adityuhkapoor/hack-mit-2026/design/pi-ui/mockup.html

# Nimbus camera UI: mockup

The Pi's 1024×600 panel in the Nimbus look (sky, pink, lime, slate; Plus Jakarta Sans). Every screen keeps its current layout and elements. This is a working prototype: tap the buttons on the panel to move through it, or jump to any screen on the left. Hold TALK to talk. Tap anywhere for a puff, and tap the viewfinder to focus.

Your camera just got an✱ Imagination ✱

✱AI CAMERA✱

shoot · it becomes one of fifty things · auto-posts

Fog rolling over a frosted field, someone holding wild chamomile

AI Camera · subject untouched, verified

POSTED

Scan to get this photo on your phone
