adityuhkapoor/hack-mit-2026/Brainstorming/HackMIT.pdf

Title | Problem | Solution | Audience & Impact | Inspiration & Research
Lego for Music Artists | Music production is locked behind expensive hardware and complicated software with a steep learning curve. This limits creativity and accessibility for beginners or low income groups wanting to learn | Modular, lego-like system that lets artists physically build and create music by snapping together interchangeable blocks for instruments, effects, tempo, mixing and more | Music Artists on the go Children Beginners | Link (https://devpost.com/software/harmoniq-p4bd9y)
AI Sticker Digi Camera/Multi Camera 3D Photos | Digital photography can feel too polished or impersonal, while alternatives like polaroids and photobooths aren't always accessible or convenient | A portable digital camera that uses AI to turn photos into personalized stickers with in-built filters and drawings AND/OR Multi camera point and shoot that click a photo at the same time - result is a photo/gif that feels like a 3D live experience | Everyone | Link #1 (https://devpost.com/software/diffuji) Link #2 (https://www.stickercamera.com/) Link #3 (https://k4mera.world/)

Other brainstorming for ideas:
Diffusion model that can recreate looks based on stuff you found on instagram and the mode selector can recreate that look for yourself

Two Parts: Hardware & Software

Hardware:
- Raspberry Pi Camera Module 3, High Quality Camera, wide-angle and autofocus camera modules
- Thermal Printer/Polaroid Printer
- Arduino Uno
- Rechargeable Battery

Electronics Diagram

Software
- World Brush: Eyedropper that captures real world textures/imagery
- Instagram Integration
- Landing Page

## Video

## Powerpoint Slides

## Script

How Does it Work - Turn Camera On - Select Mode: World Brush OR Filters - World Brush - Point at a texture and hold down a button for 3 seconds to lock it in - Then Take Picture - Then use brush to draw on picture - Filter - Select Filter - Then Take Picture - Image Processing - Press Confirm - Prints Picture Physical Format - Auto Uploads to Instagram Story/Feed - Camera Off
