adityuhkapoor/hack-mit-2026/docs/demo/video/README.md

# Demo renders for the video

Four scenes through the live pipeline on the GB10 (klein 9B, 1.0 MP), Muse choosing the format unprompted:

| Scene | Muse chose | Headline | Source photo |
|---|---|---|---|
| kids playing football | sports trading card | ROOKIE HYPE TEN | US Army / Rachel Larue, public domain |
| slurping ramen, Dōtonbori | instant noodle packet | MIDNIGHT SHOYU SLURP | Maarten Heerlien, CC BY 2.0 |
| guitarist in the woods | music album cover | FOREST SHREDDER | Mostafameraji, CC BY 4.0 |
| study area | school detention slip | SILENT DETENTION HALL | D00264450, CC BY-SA 4.0 |

`*-as-shot.jpg` is the input, `*-nimbus.jpg` the square print, `*-before-after.jpg` both side by side (1080 px
tall). The people are pixel-identical between the two — "subject unaltered · verified" on every one.
