adityuhkapoor/hack-mit-2026/archive/pitch/hackmit-sketch.pdf

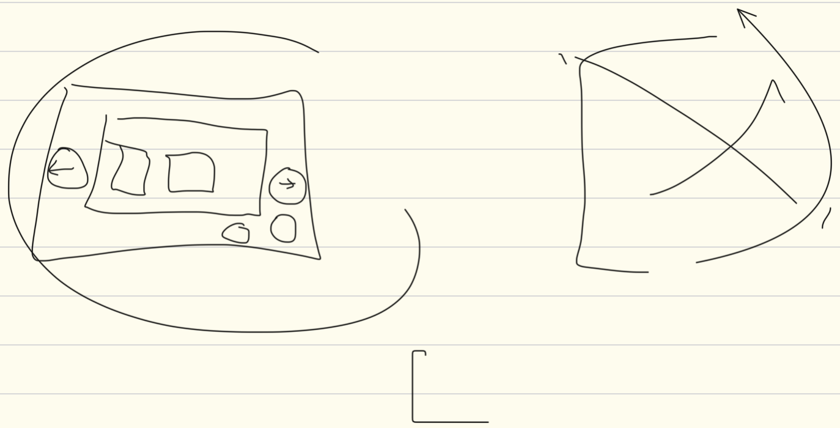
[picture p2: figure]
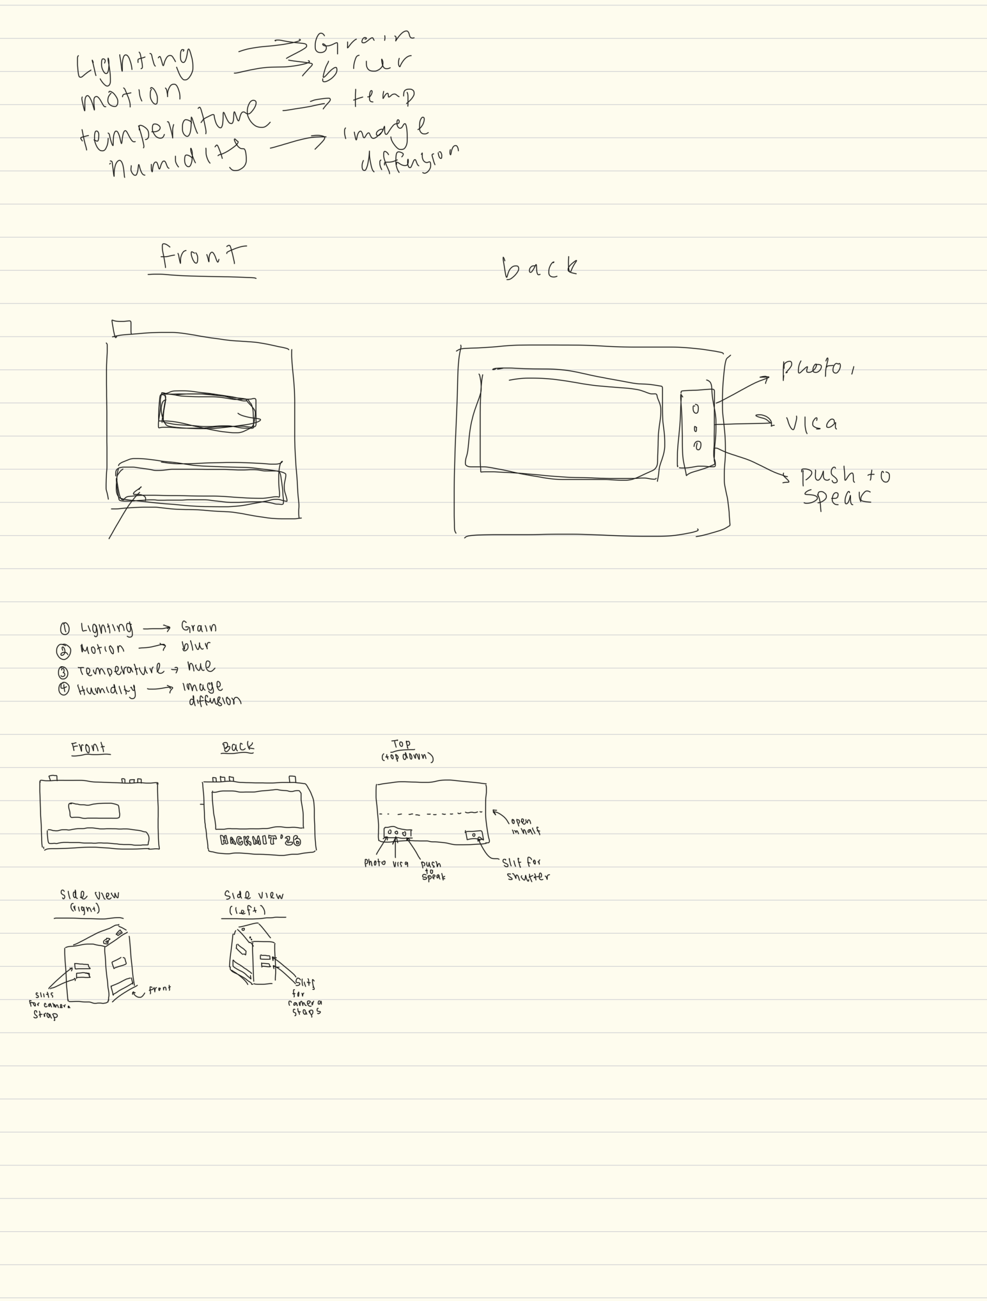
[picture p3: page 2]
