adityuhkapoor/hack-mit-2026/Brainstorming/Pasted 2026-09-18 at 11.16.00 PM.png

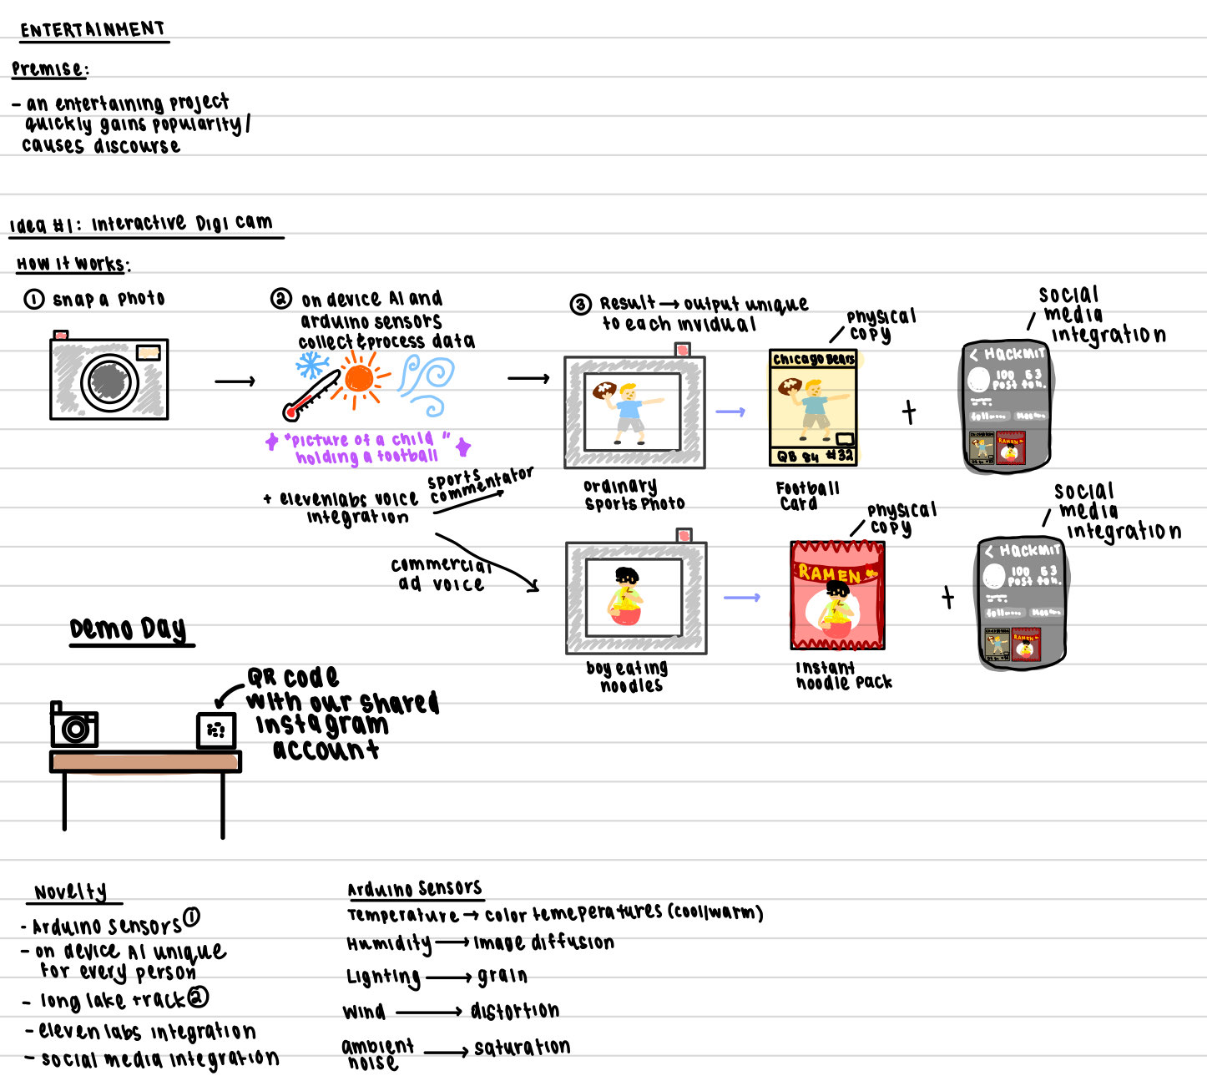
Brainstorming/Pasted 2026-09-18 at 11.16.00 PM.png
