adityuhkapoor/hack-mit-2026/design/modular-camera/cutaway.png

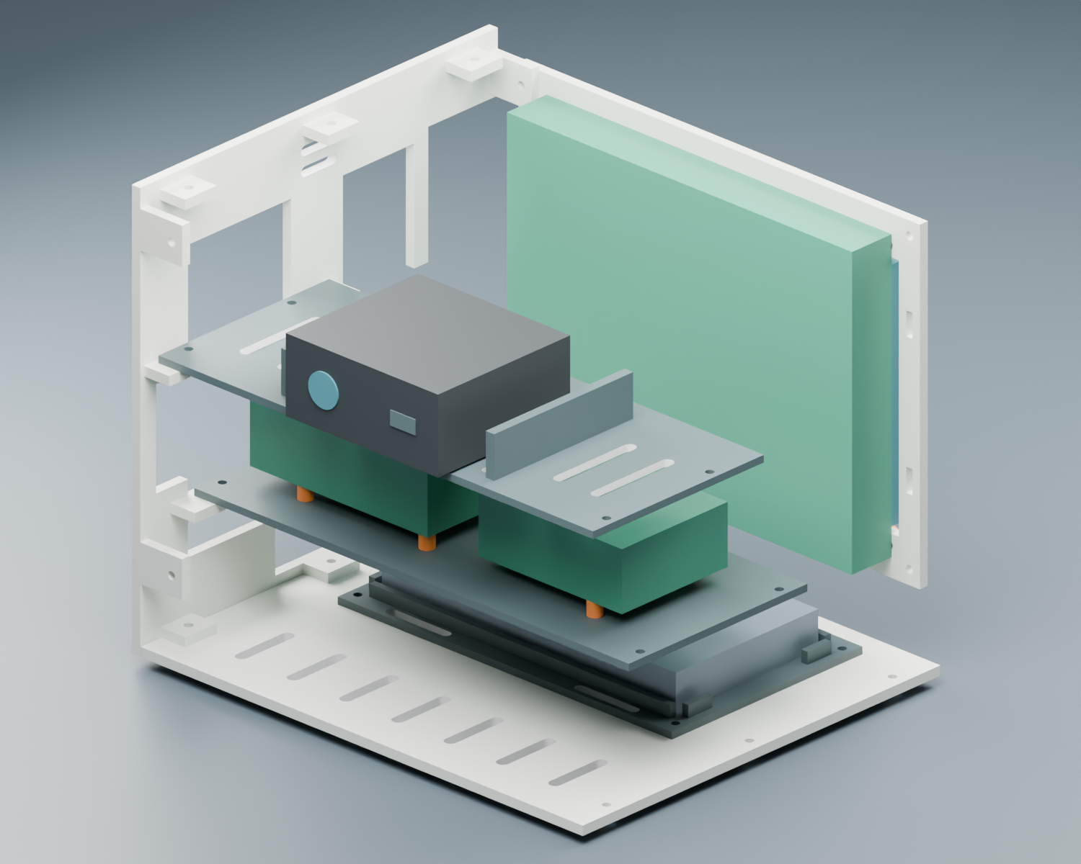
design/modular-camera/cutaway.png
