adityuhkapoor/hack-mit-2026/docs/demo/dusk_0_as_shot.jpg

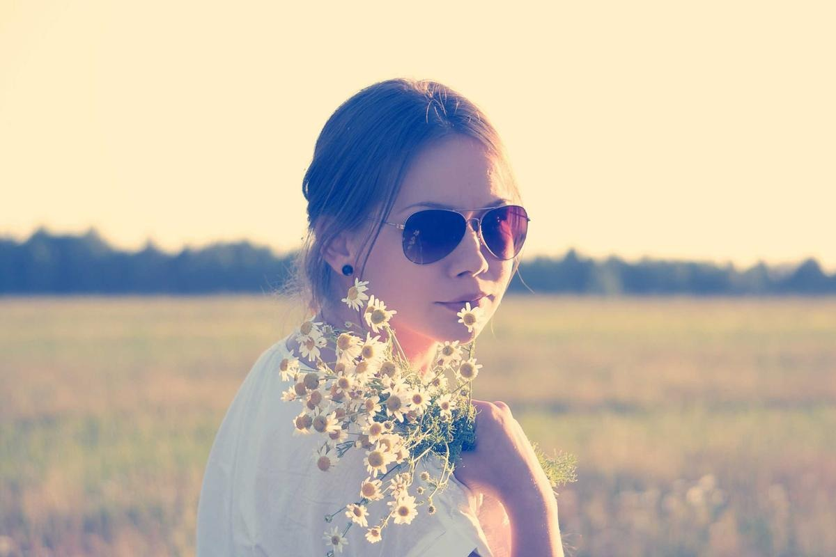
docs/demo/dusk_0_as_shot.jpg
