adityuhkapoor/hack-mit-2026/docs/demo/dusk_0_card.jpg

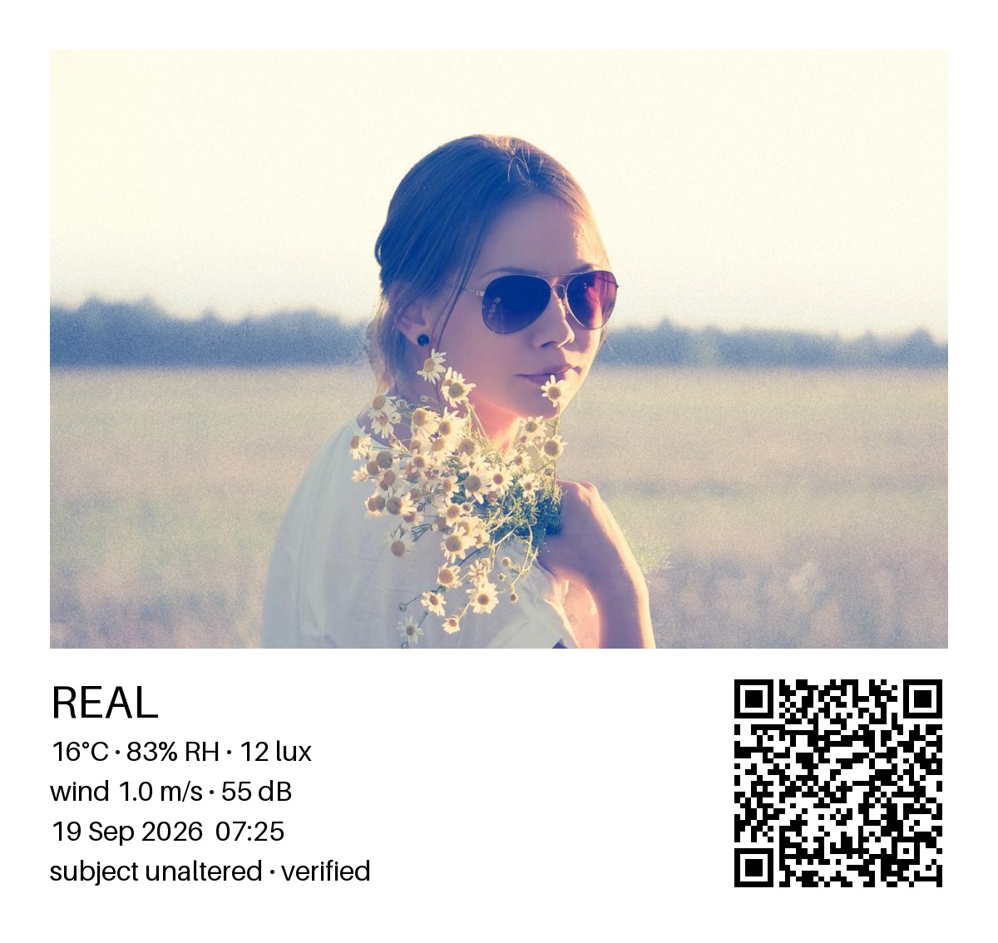
docs/demo/dusk_0_card.jpg
