adityuhkapoor/hack-mit-2026/docs/demo/dusk_0_photo.jpg

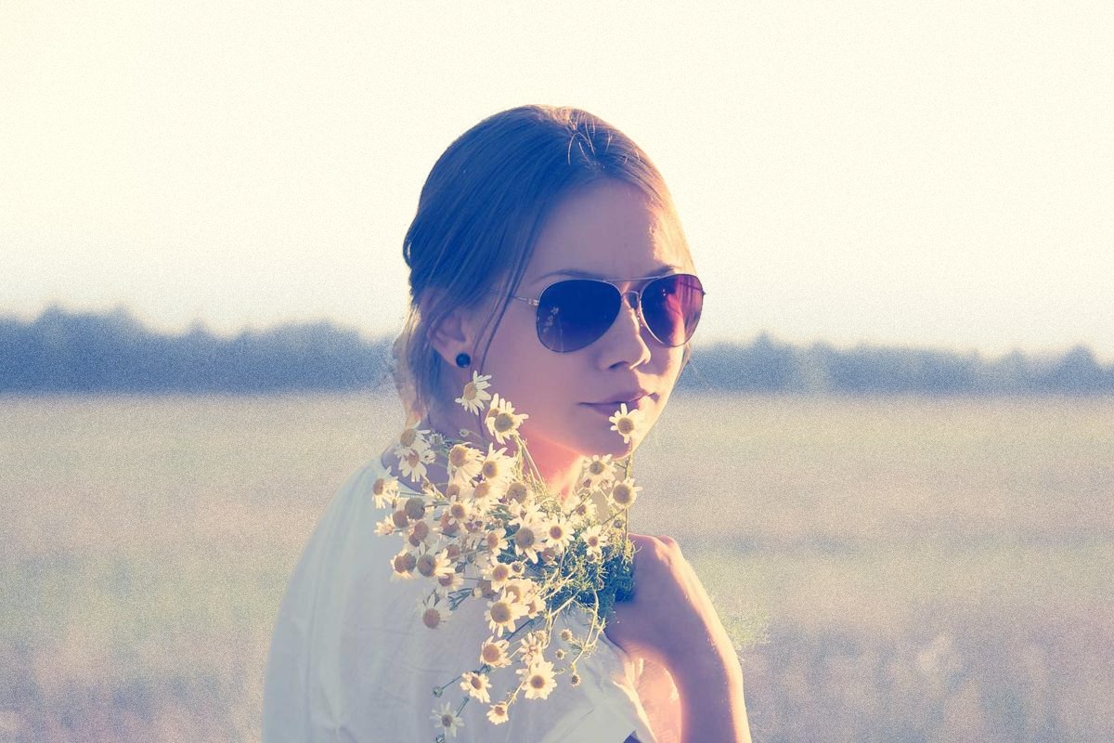
docs/demo/dusk_0_photo.jpg
