adityuhkapoor/hack-mit-2026/docs/demo/dusk_1_card.jpg

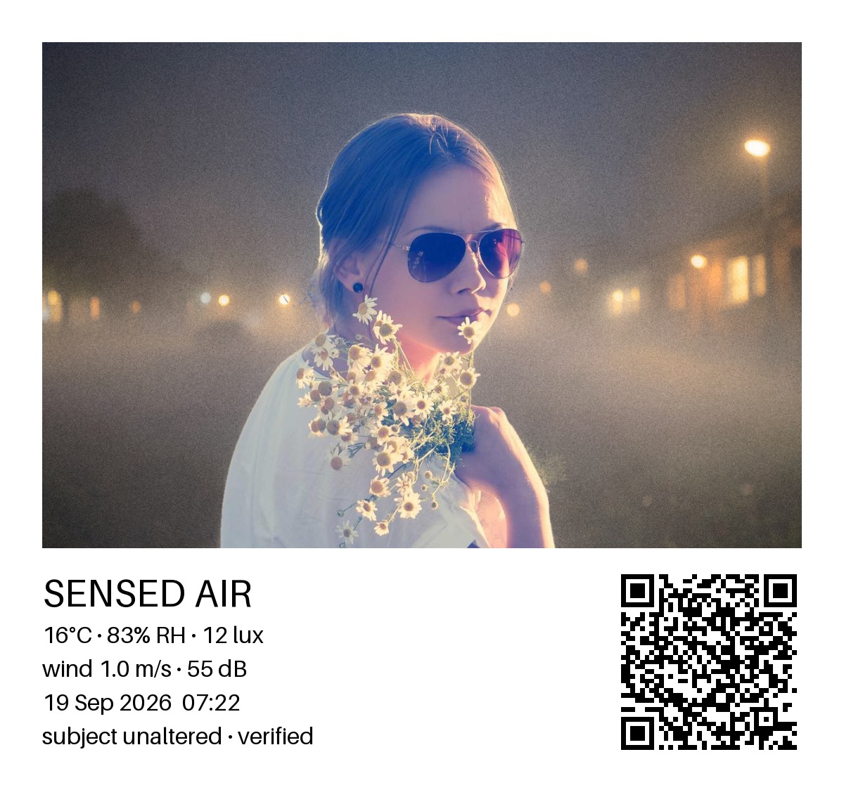
docs/demo/dusk_1_card.jpg
