adityuhkapoor/hack-mit-2026/docs/demo/dusk_1_photo.jpg

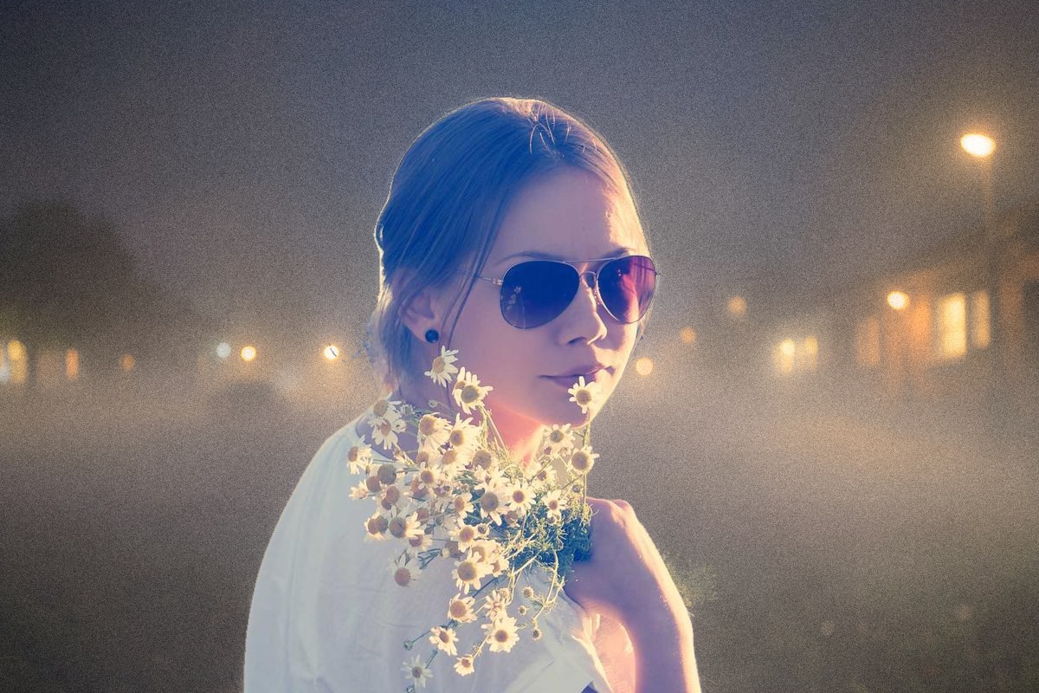
docs/demo/dusk_1_photo.jpg
