adityuhkapoor/hack-mit-2026/docs/demo/dusk_2_photo.jpg

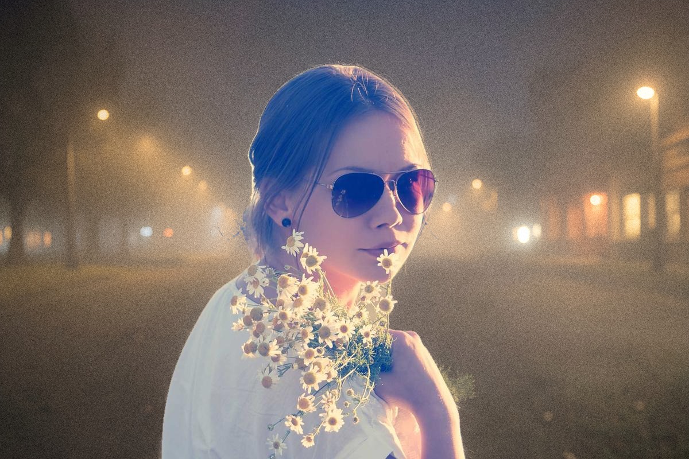
docs/demo/dusk_2_photo.jpg
