adityuhkapoor/hack-mit-2026/docs/demo/fog_0_photo.jpg

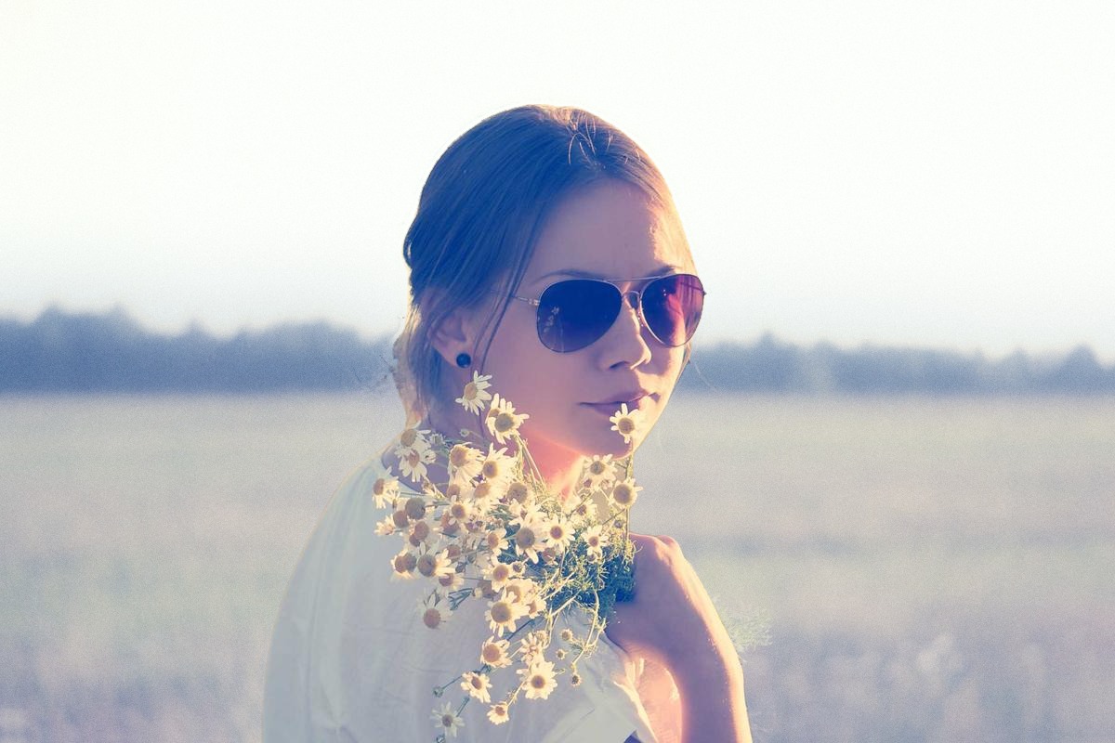
docs/demo/fog_0_photo.jpg
