adityuhkapoor/hack-mit-2026/docs/demo/fog_1_card.jpg

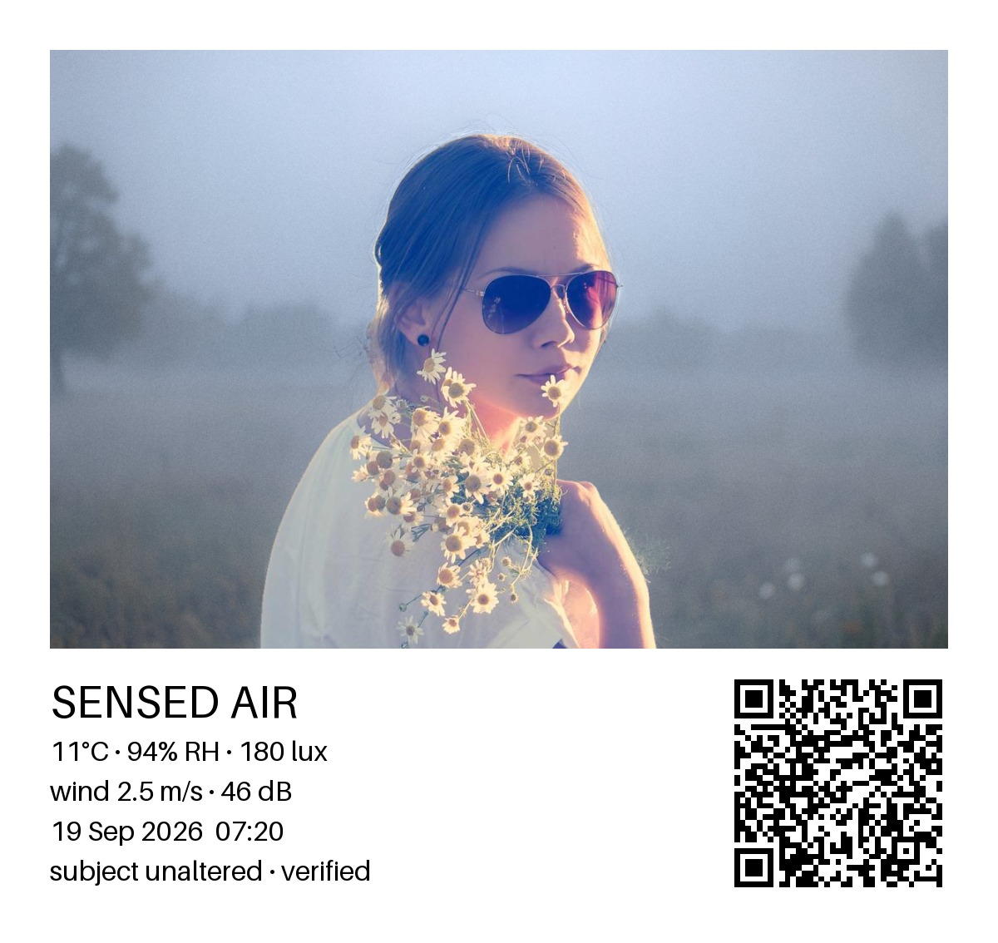
docs/demo/fog_1_card.jpg
