adityuhkapoor/hack-mit-2026/docs/demo/fog_1_photo.jpg

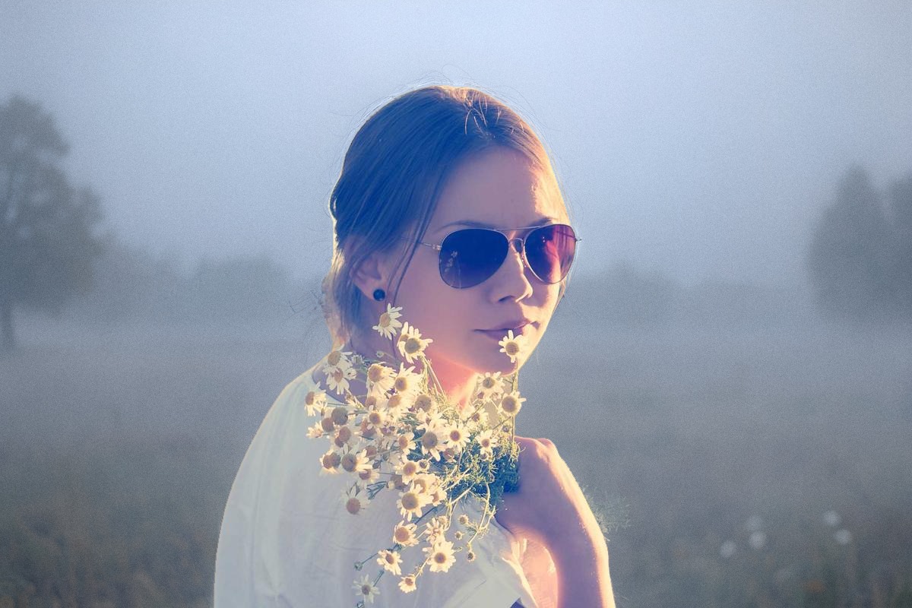
docs/demo/fog_1_photo.jpg
