adityuhkapoor/hack-mit-2026/docs/demo/fog_2_card.jpg

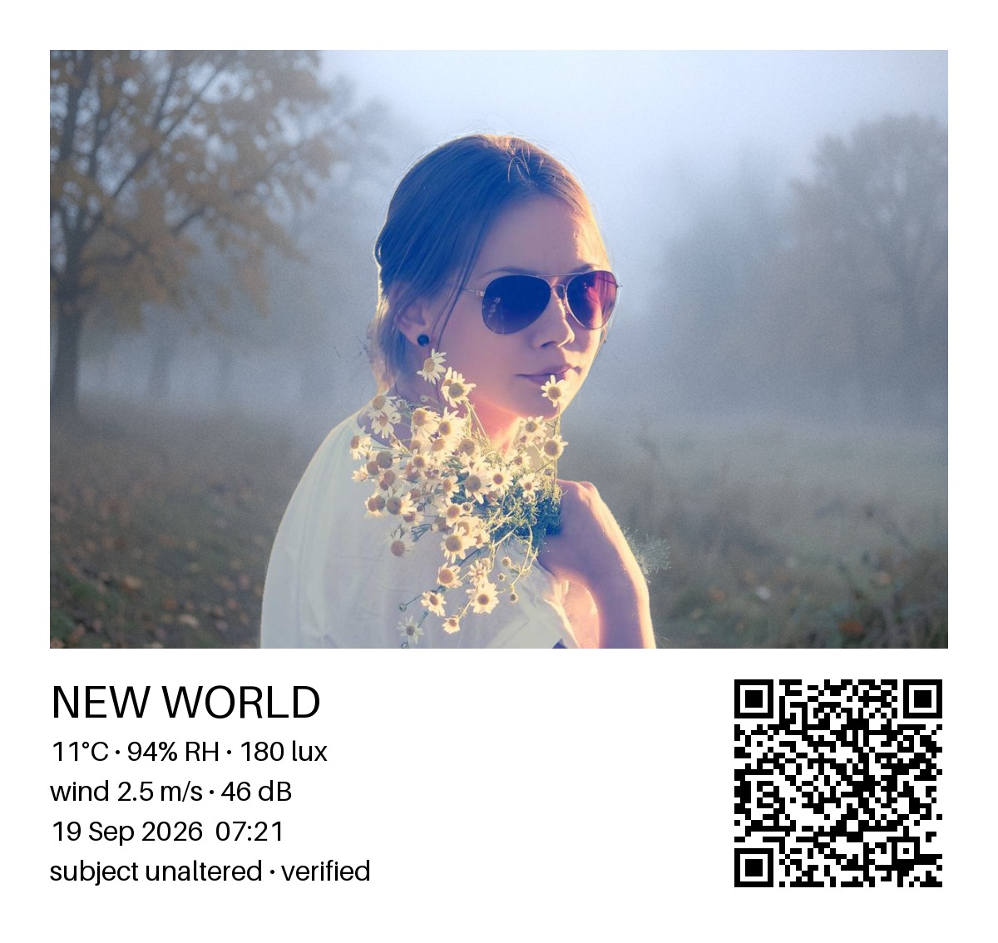
docs/demo/fog_2_card.jpg
