adityuhkapoor/hack-mit-2026/docs/demo/fog_2_photo.jpg

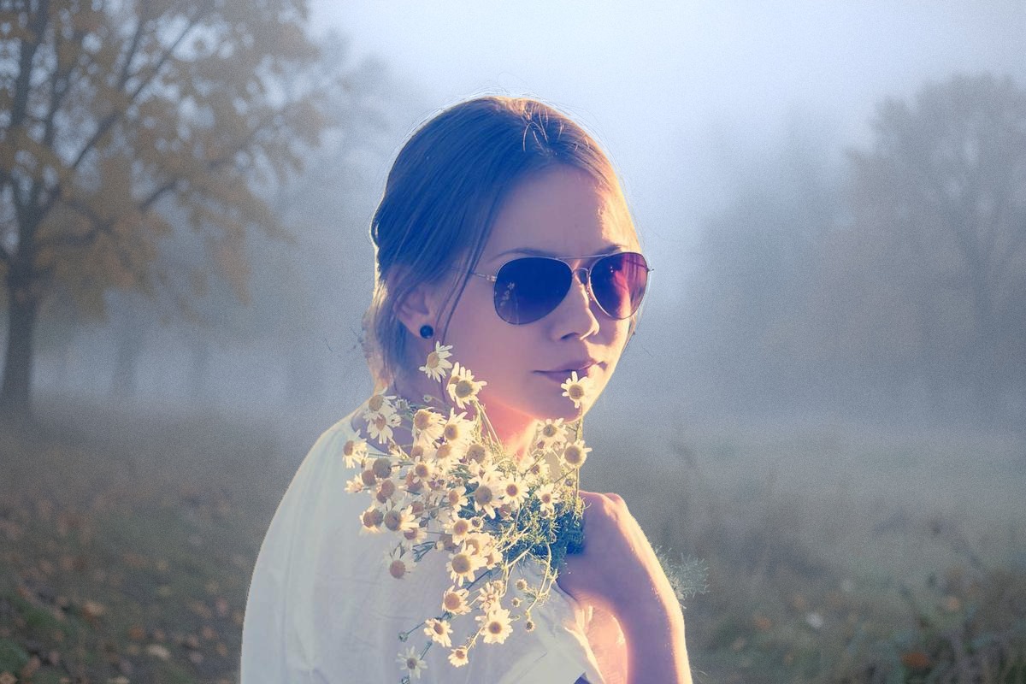
docs/demo/fog_2_photo.jpg
