adityuhkapoor/hack-mit-2026/docs/demo/heat_0_card.jpg

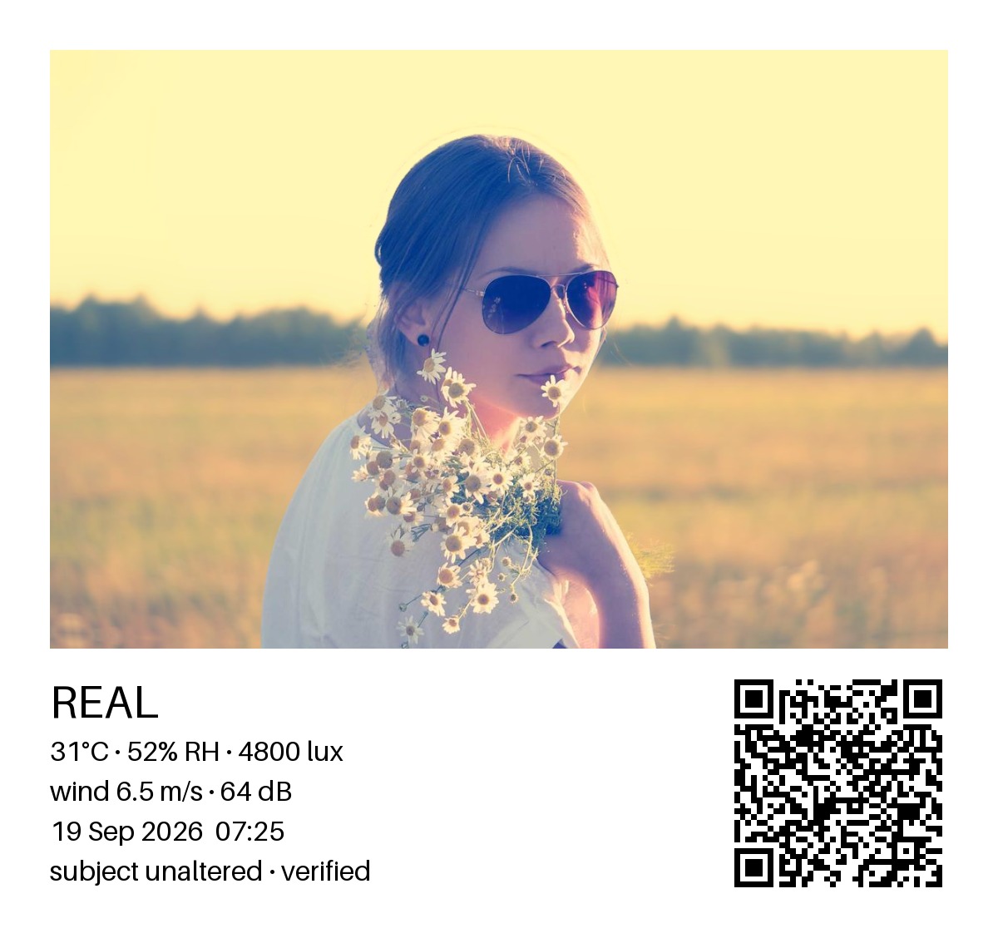
docs/demo/heat_0_card.jpg
