adityuhkapoor/hack-mit-2026/docs/demo/heat_1_card.jpg

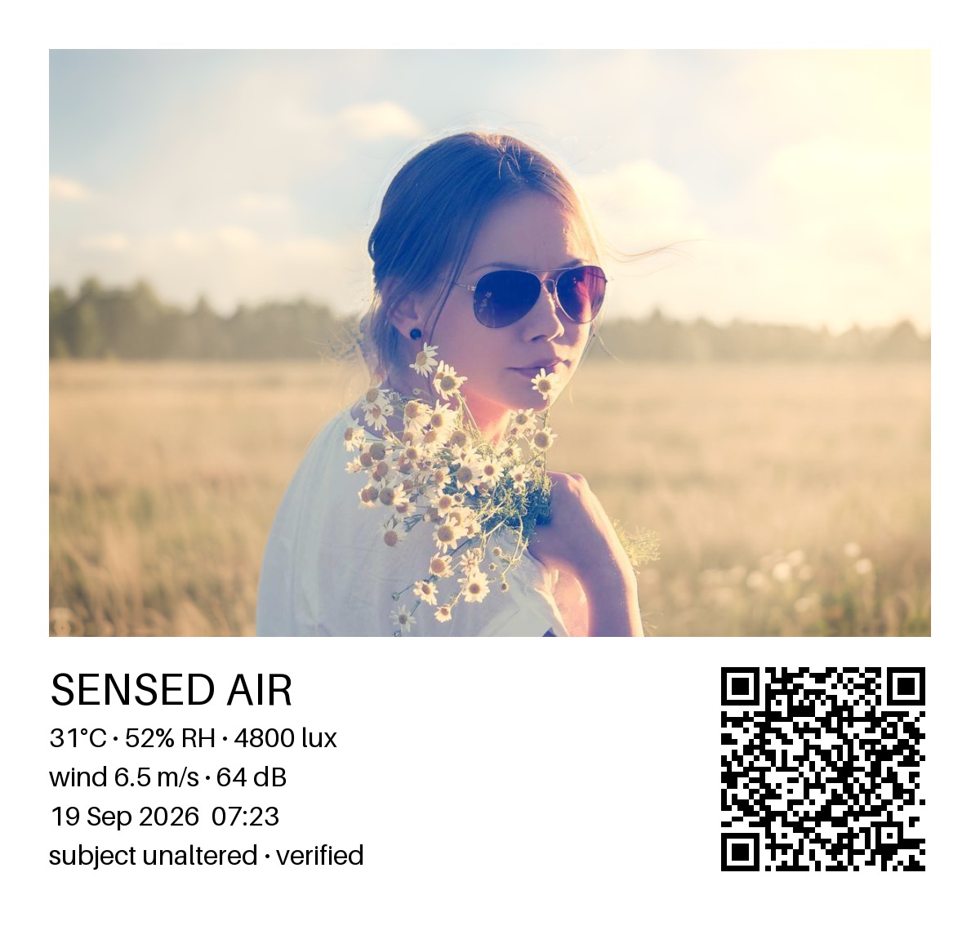
docs/demo/heat_1_card.jpg
