adityuhkapoor/hack-mit-2026/docs/demo/heat_1_photo.jpg

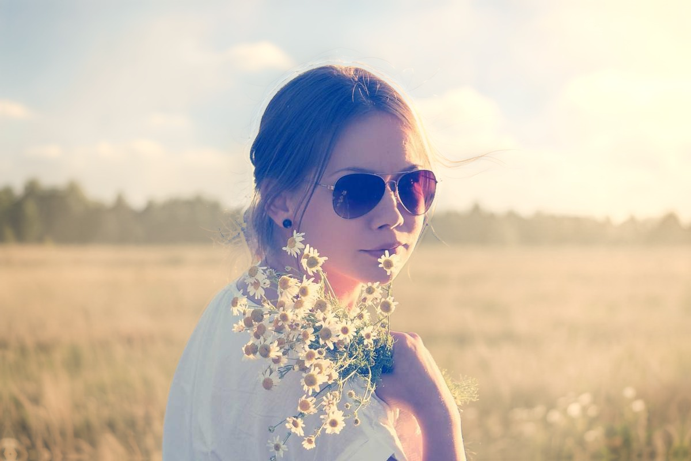
docs/demo/heat_1_photo.jpg
