adityuhkapoor/hack-mit-2026/docs/demo/heat_2_card.jpg

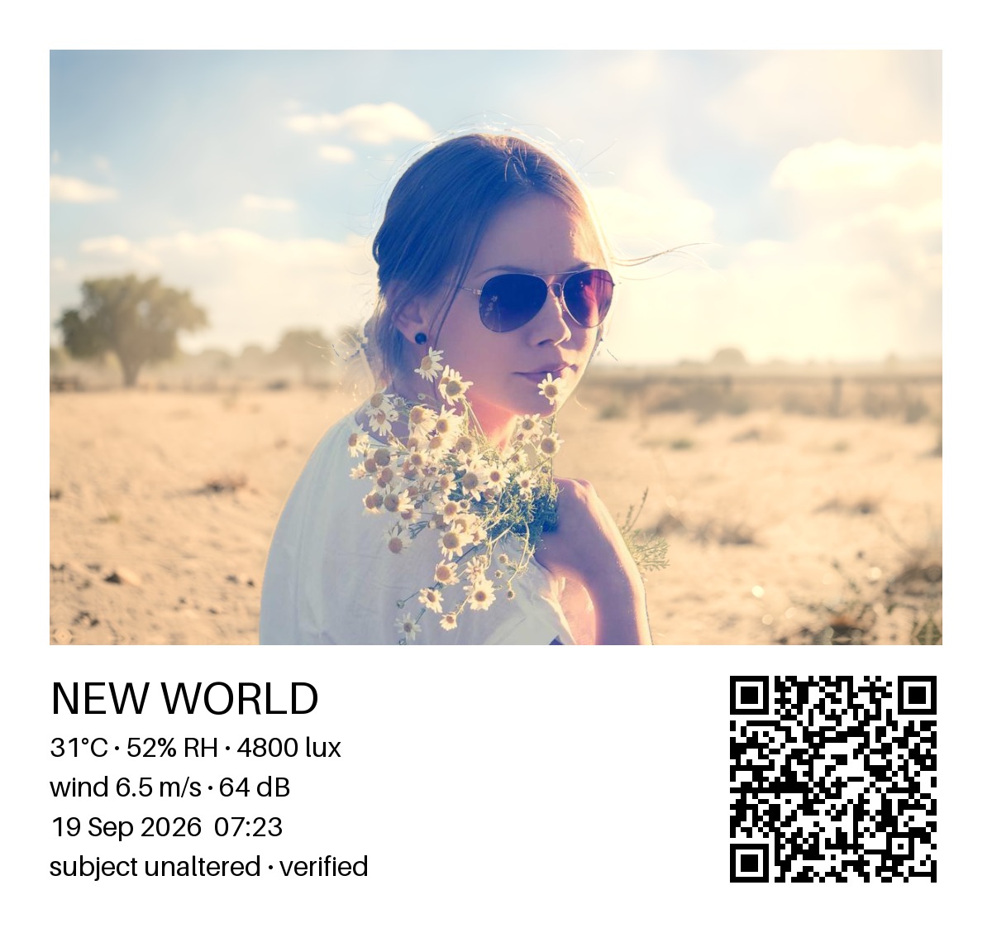
docs/demo/heat_2_card.jpg
