adityuhkapoor/hack-mit-2026/docs/demo/heat_2_photo.jpg

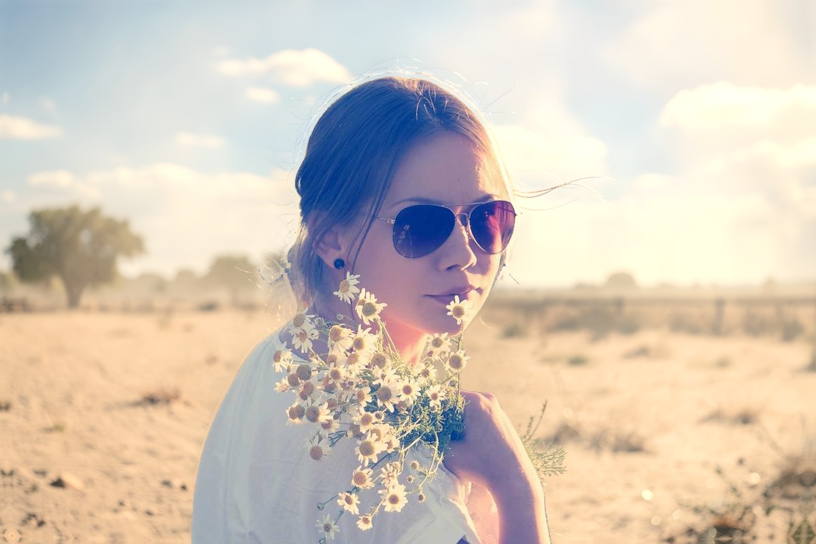
docs/demo/heat_2_photo.jpg
