adityuhkapoor/hack-mit-2026/docs/demo/pi-panel.png

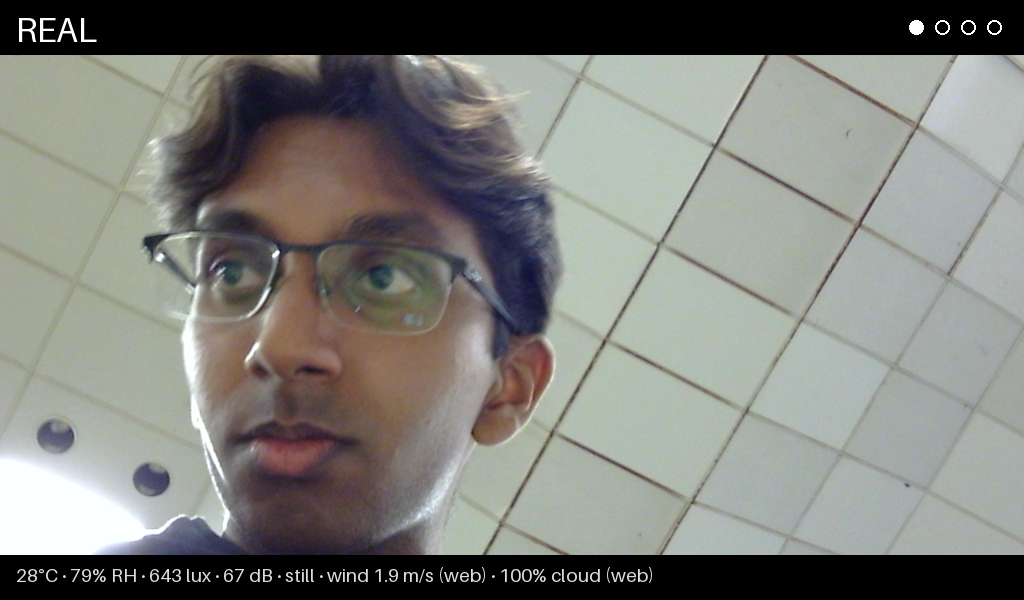
docs/demo/pi-panel.png
