adityuhkapoor/hack-mit-2026/docs/demo/sheet.jpg

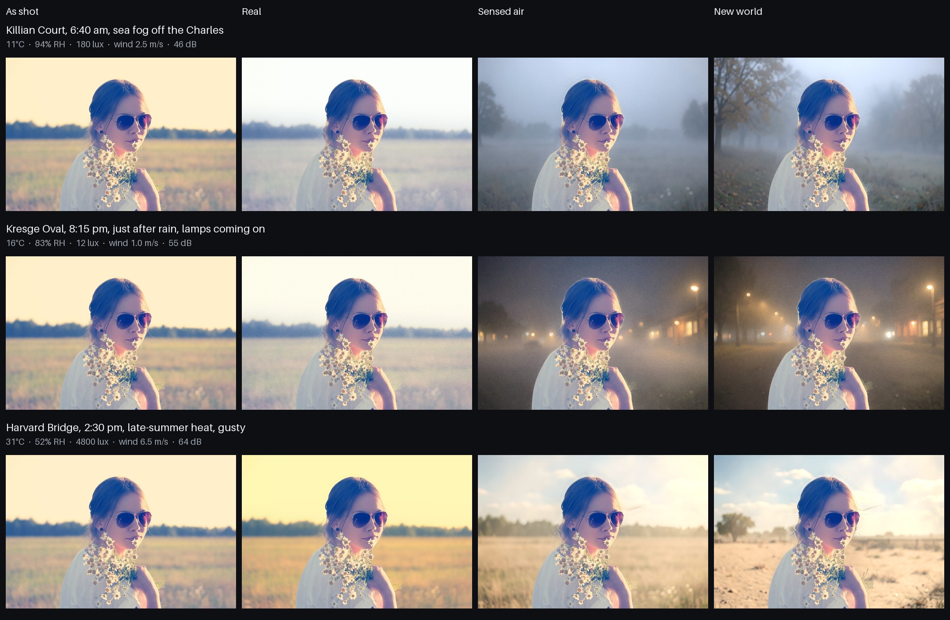
docs/demo/sheet.jpg
