adityuhkapoor/hack-mit-2026/docs/demo/video/football-as-shot.jpg

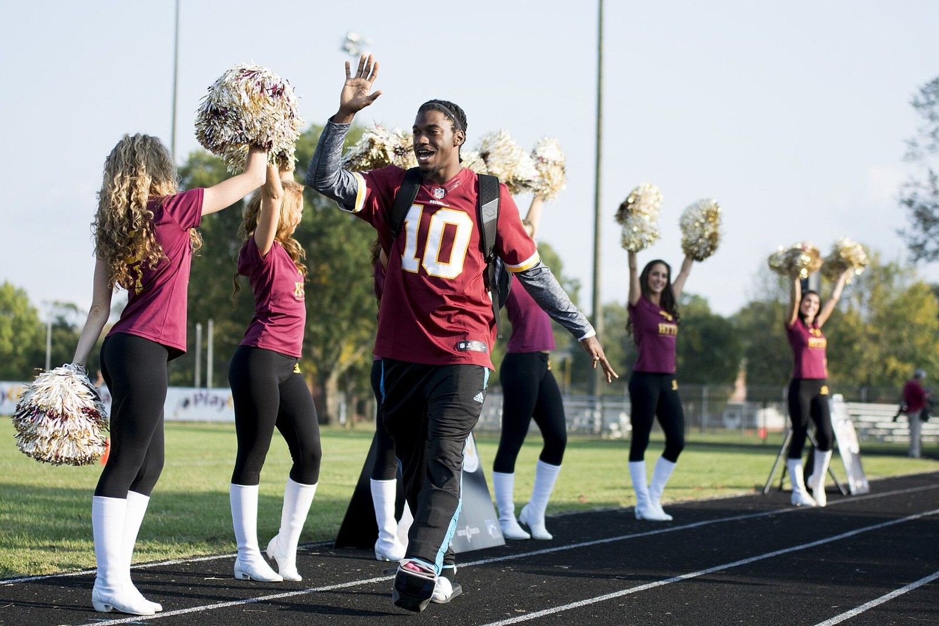
docs/demo/video/football-as-shot.jpg
