adityuhkapoor/hack-mit-2026/docs/demo/video/football-before-after.jpg

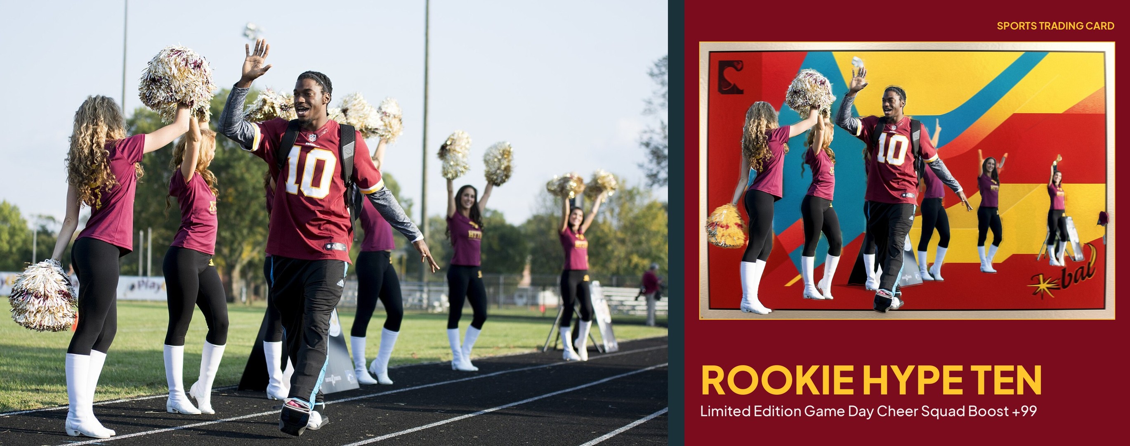
docs/demo/video/football-before-after.jpg
