adityuhkapoor/hack-mit-2026/docs/demo/video/football-nimbus.jpg

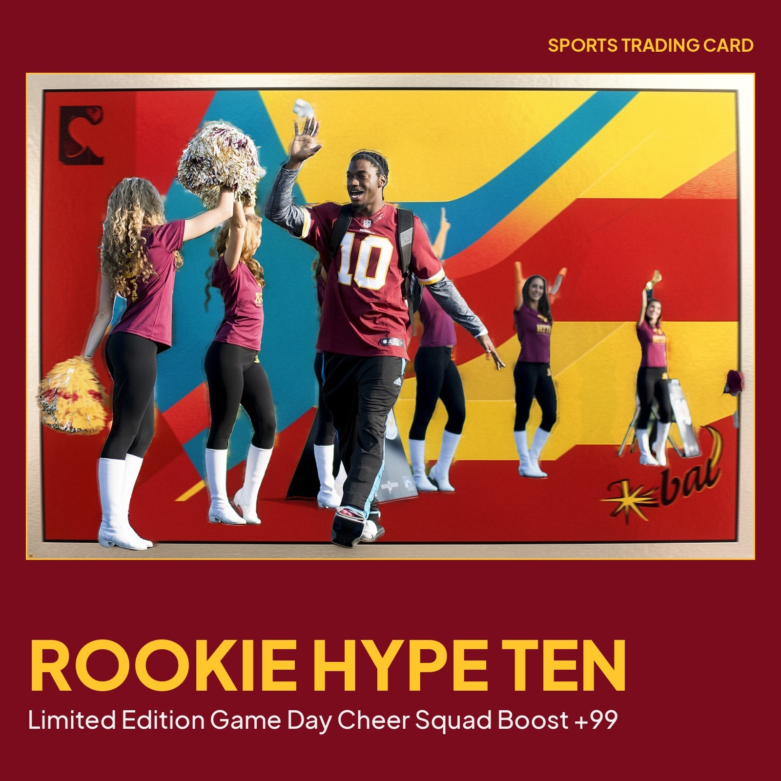
docs/demo/video/football-nimbus.jpg
