adityuhkapoor/hack-mit-2026/docs/demo/video/guitar-as-shot.jpg

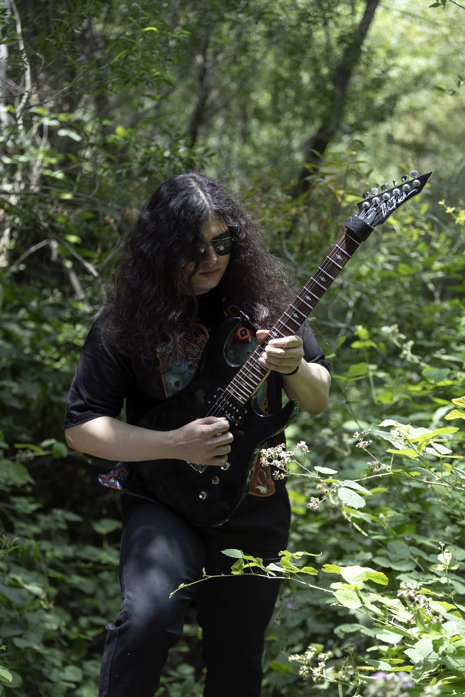
docs/demo/video/guitar-as-shot.jpg
