adityuhkapoor/hack-mit-2026/docs/demo/video/guitar-before-after.jpg

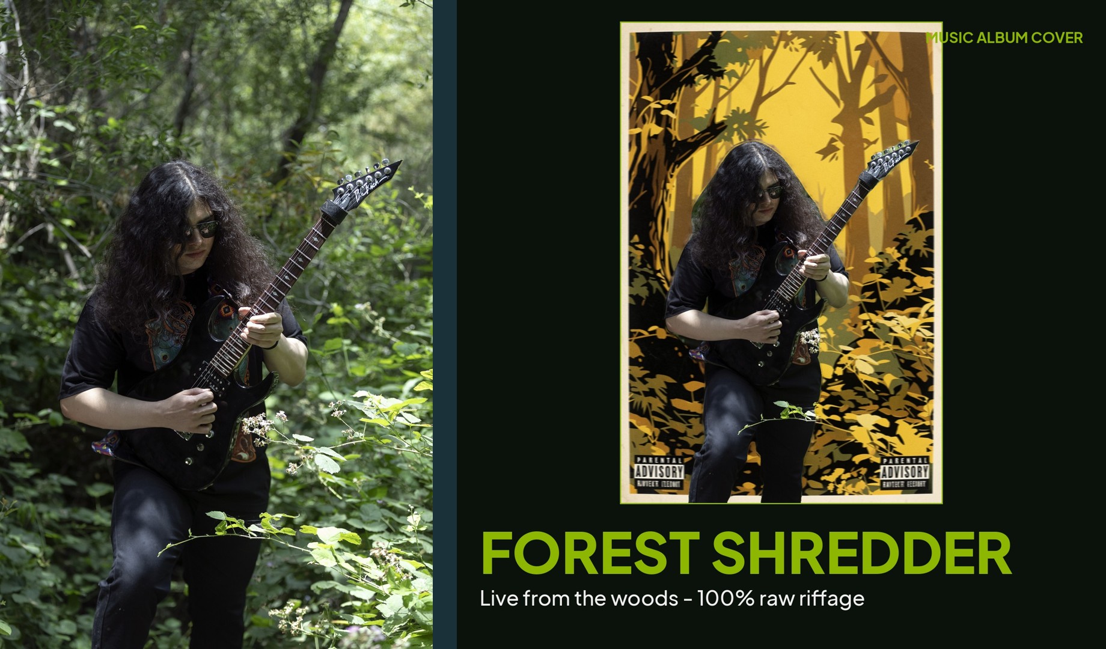
docs/demo/video/guitar-before-after.jpg
