adityuhkapoor/hack-mit-2026/docs/demo/video/guitar-nimbus.jpg

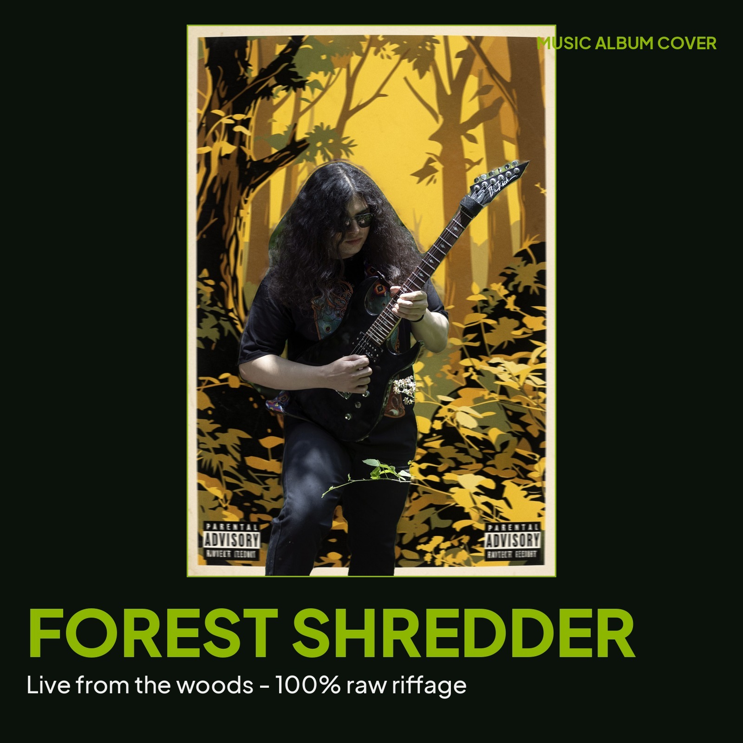
docs/demo/video/guitar-nimbus.jpg
