adityuhkapoor/hack-mit-2026/docs/demo/video/ramen-as-shot.jpg

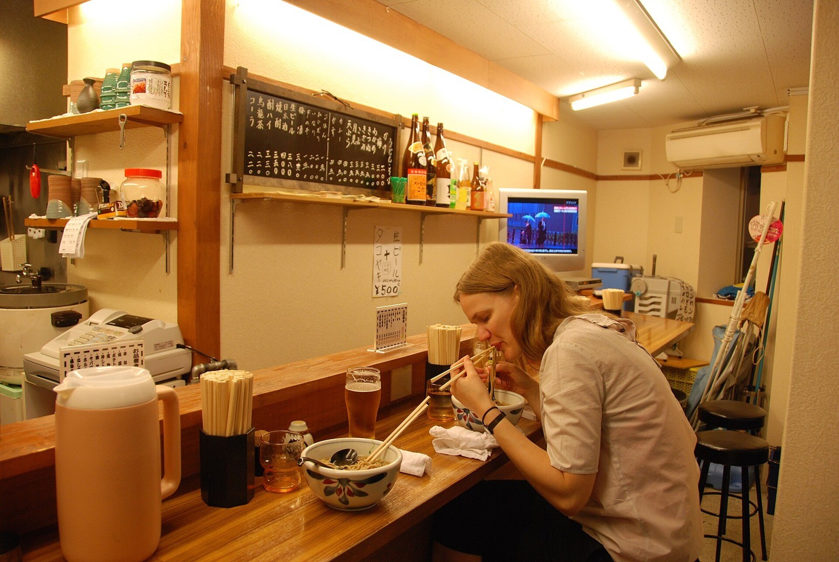
docs/demo/video/ramen-as-shot.jpg
