adityuhkapoor/hack-mit-2026/docs/demo/video/ramen-before-after.jpg

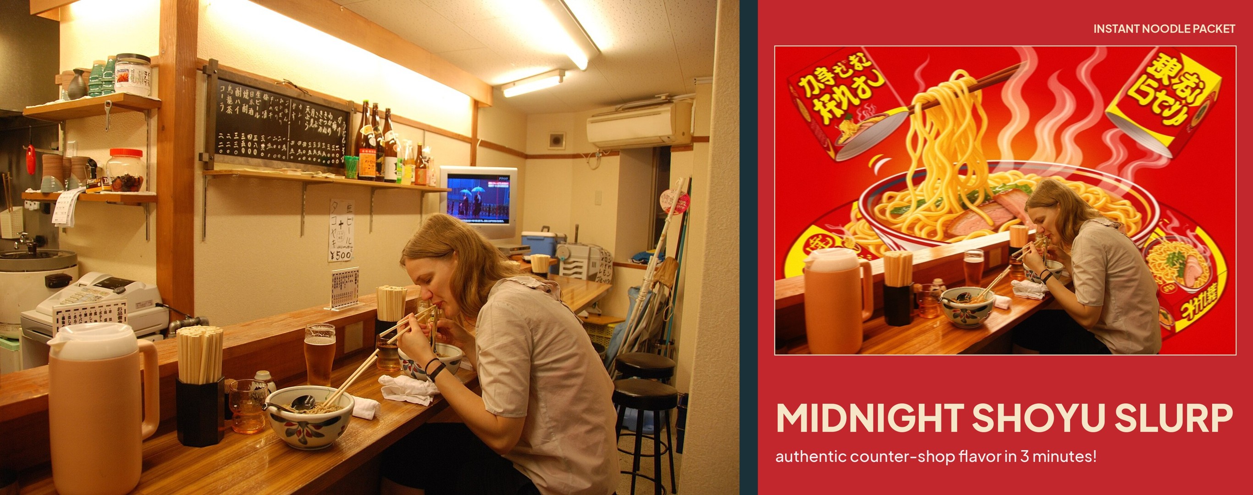
docs/demo/video/ramen-before-after.jpg
