adityuhkapoor/hack-mit-2026/docs/demo/video/ramen-nimbus.jpg

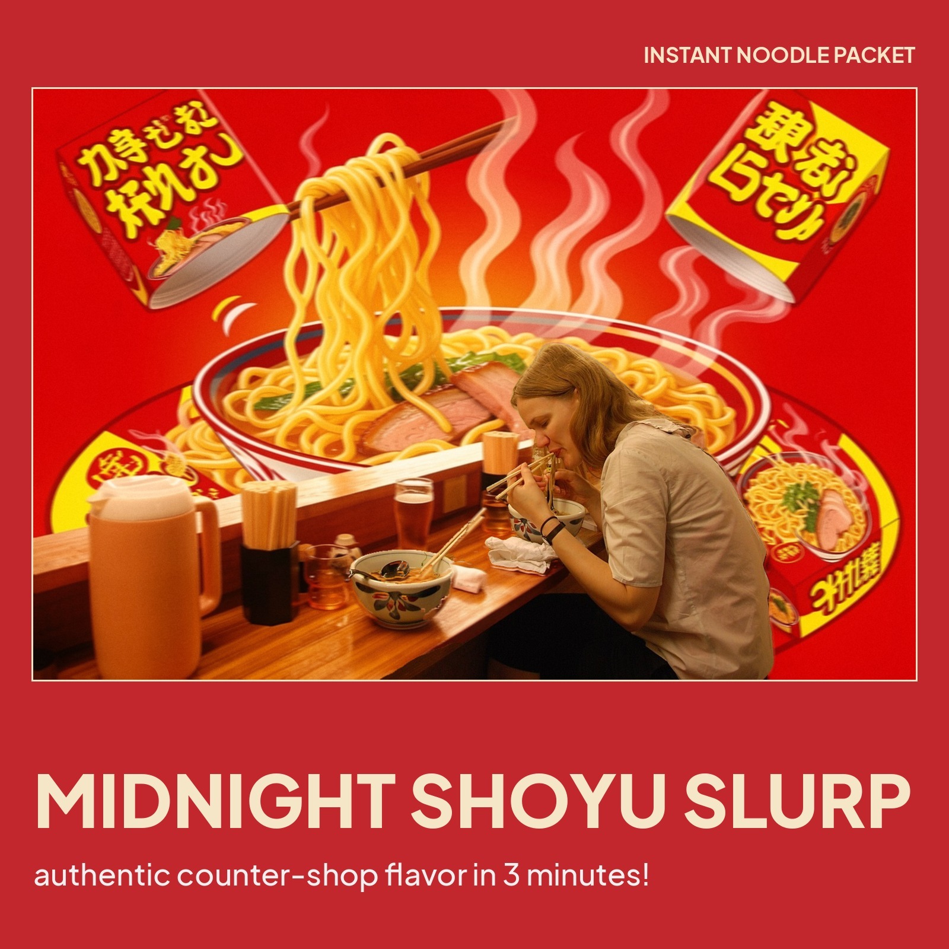
docs/demo/video/ramen-nimbus.jpg
