adityuhkapoor/hack-mit-2026/docs/demo/video/study-as-shot.jpg

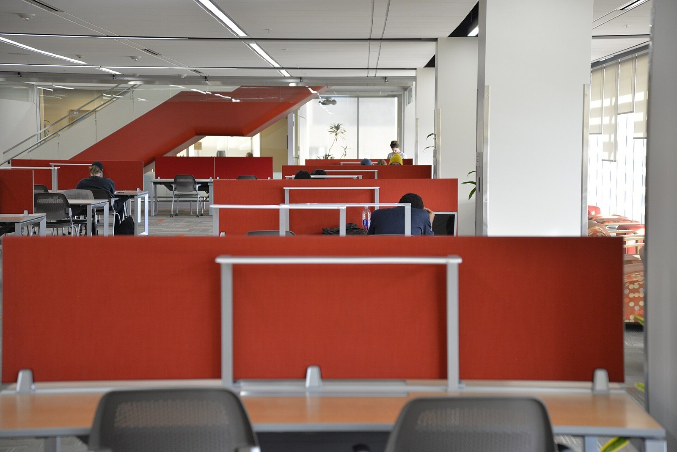
docs/demo/video/study-as-shot.jpg
