adityuhkapoor/hack-mit-2026/docs/demo/video/study-before-after.jpg

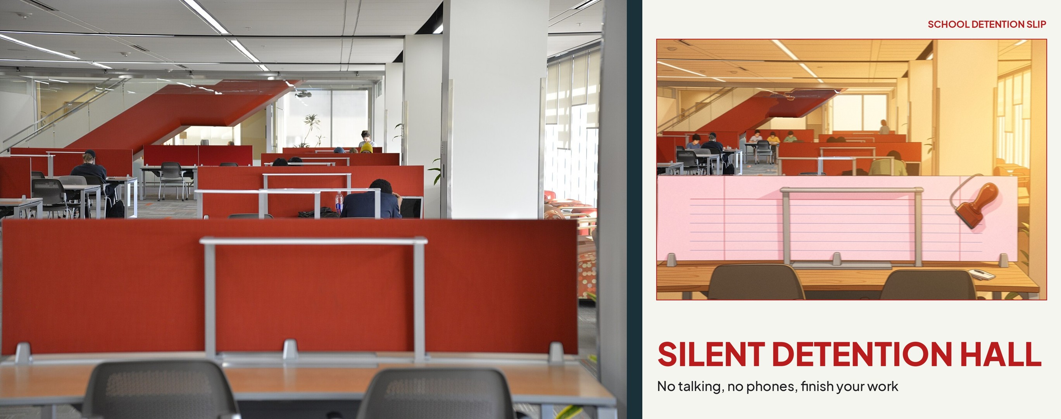
docs/demo/video/study-before-after.jpg
