adityuhkapoor/hack-mit-2026/docs/demo/video/study-nimbus.jpg

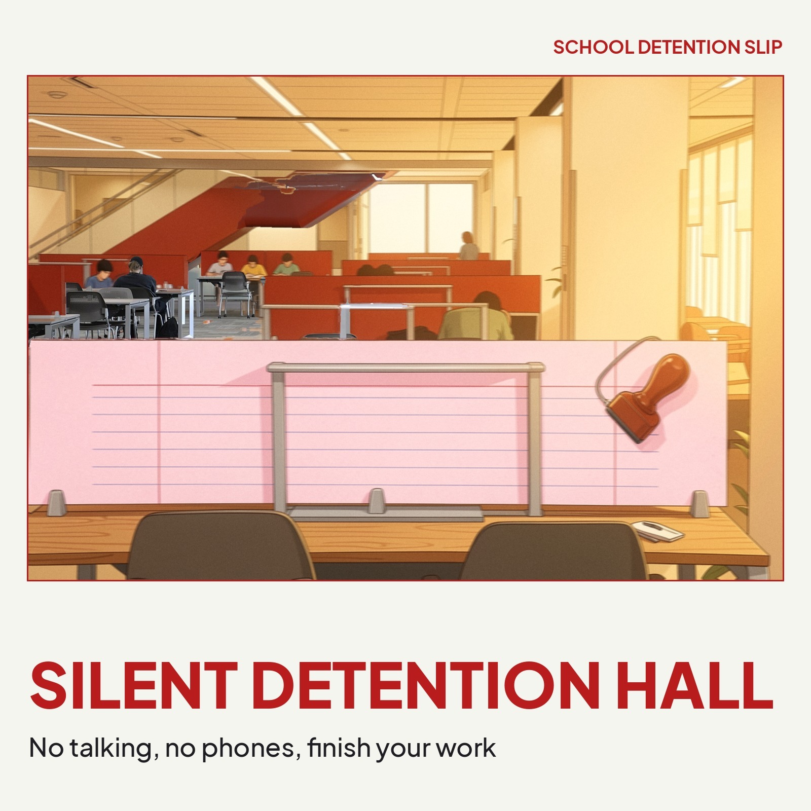
docs/demo/video/study-nimbus.jpg
