adityuhkapoor/hack-mit-2026/Photos/DSC00272-Enhanced-NR.JPG

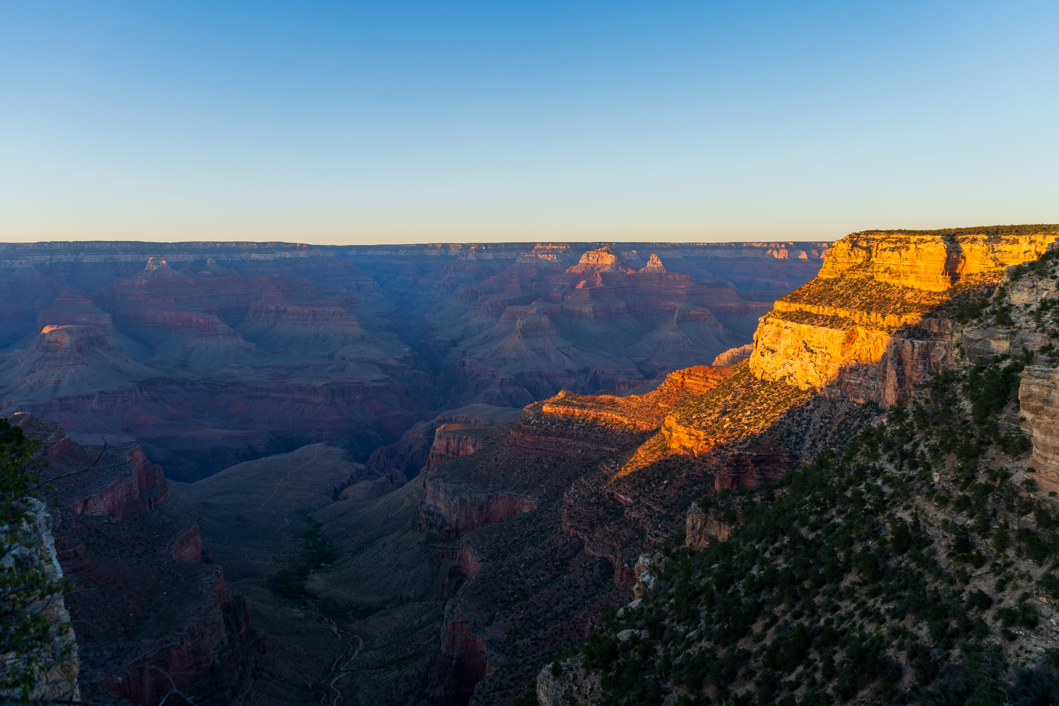
Photos/DSC00272-Enhanced-NR.JPG
