adityuhkapoor/hack-mit-2026/Photos/DSC06684-Enhanced-NR.JPG

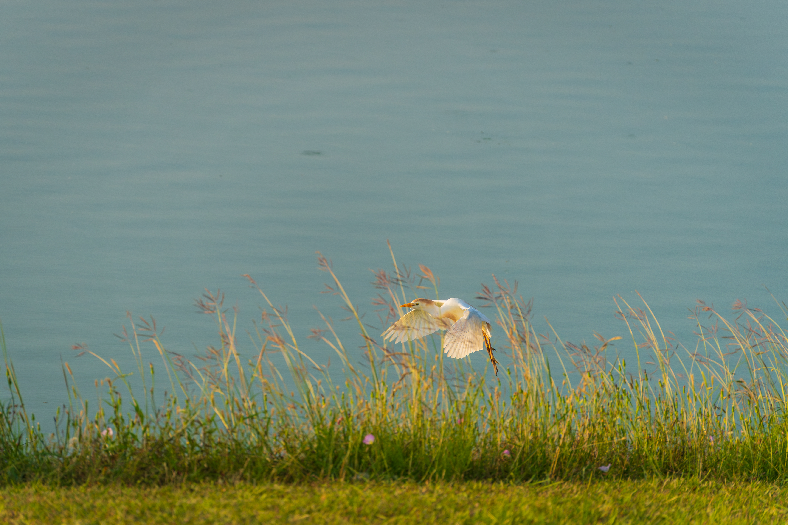
Photos/DSC06684-Enhanced-NR.JPG
