adityuhkapoor/hack-mit-2026/Photos/looks/_DSC7022-Enhanced-NR/00_original.jpg

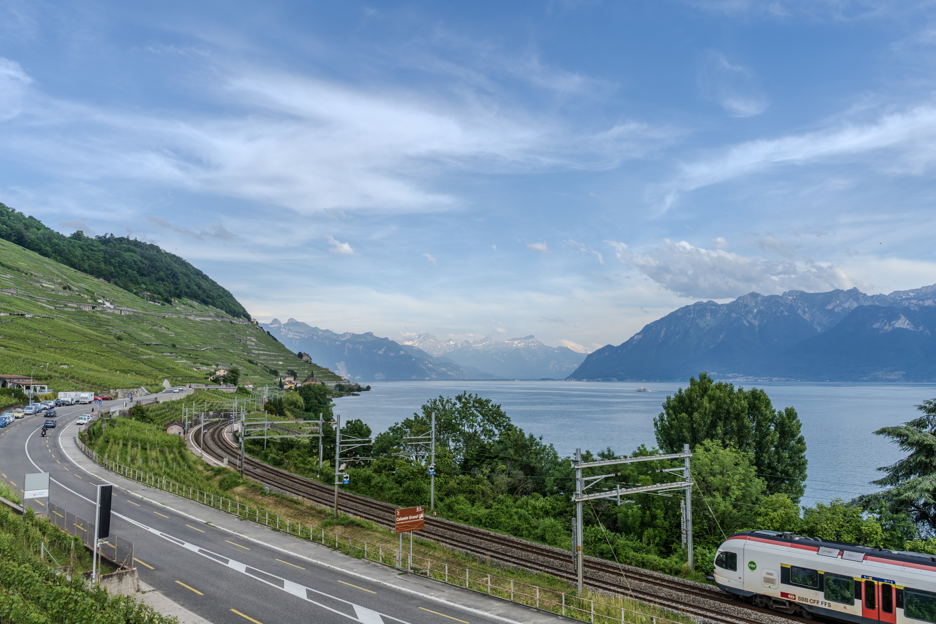
Photos/looks/_DSC7022-Enhanced-NR/00_original.jpg
