adityuhkapoor/hack-mit-2026/Photos/looks/_DSC7022-Enhanced-NR/06_digicam.jpg

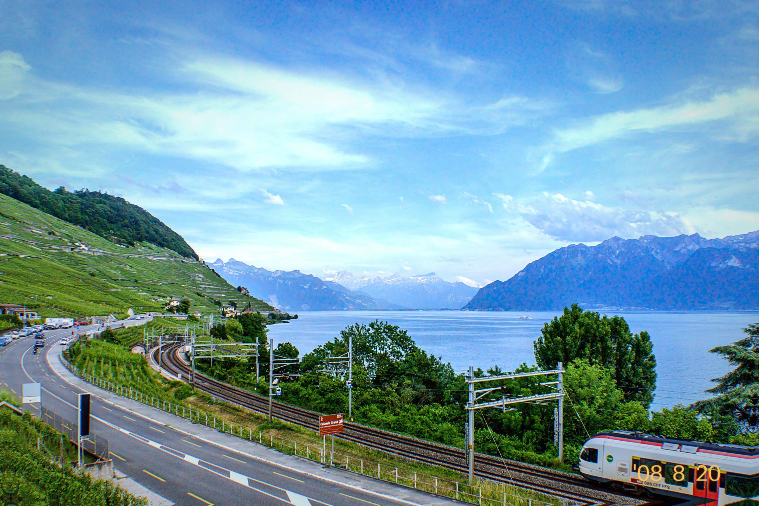
Photos/looks/_DSC7022-Enhanced-NR/06_digicam.jpg
