adityuhkapoor/hack-mit-2026/Photos/looks/_DSC7022-Enhanced-NR/08_instant.jpg

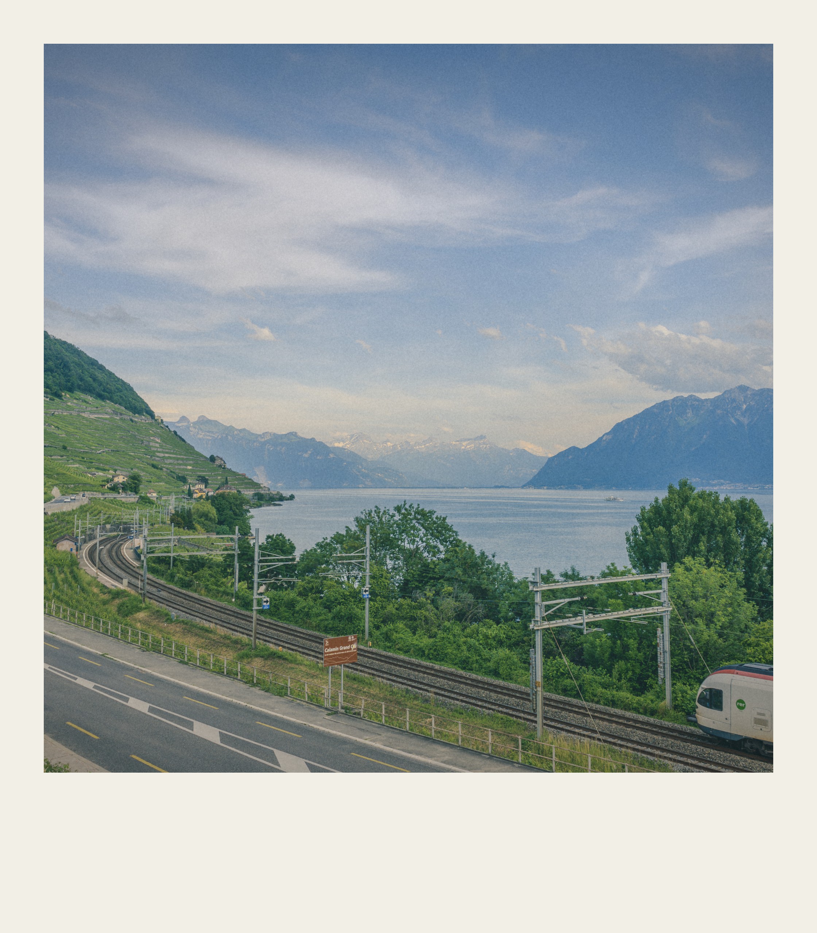
Photos/looks/_DSC7022-Enhanced-NR/08_instant.jpg
