adityuhkapoor/hack-mit-2026/Photos/looks/_DSC7022-Enhanced-NR/11_anime.jpg

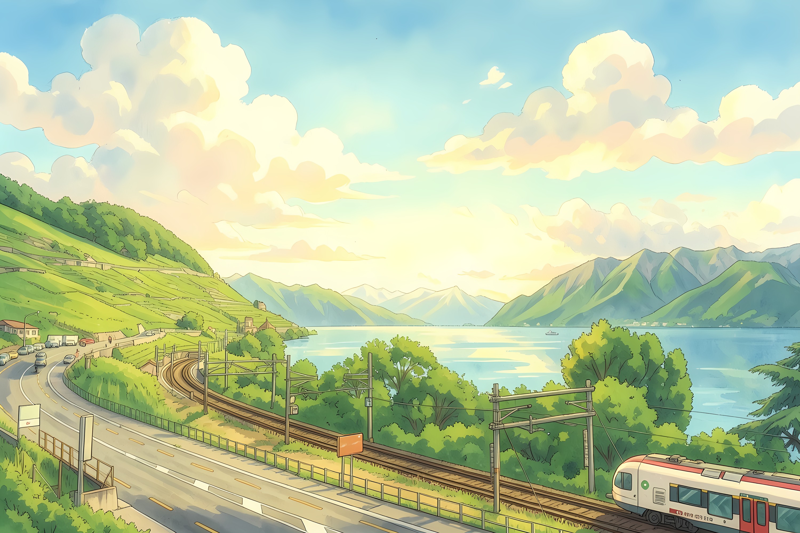
Photos/looks/_DSC7022-Enhanced-NR/11_anime.jpg
