adityuhkapoor/hack-mit-2026/Photos/looks/_DSC7022-Enhanced-NR/12_watercolor.jpg

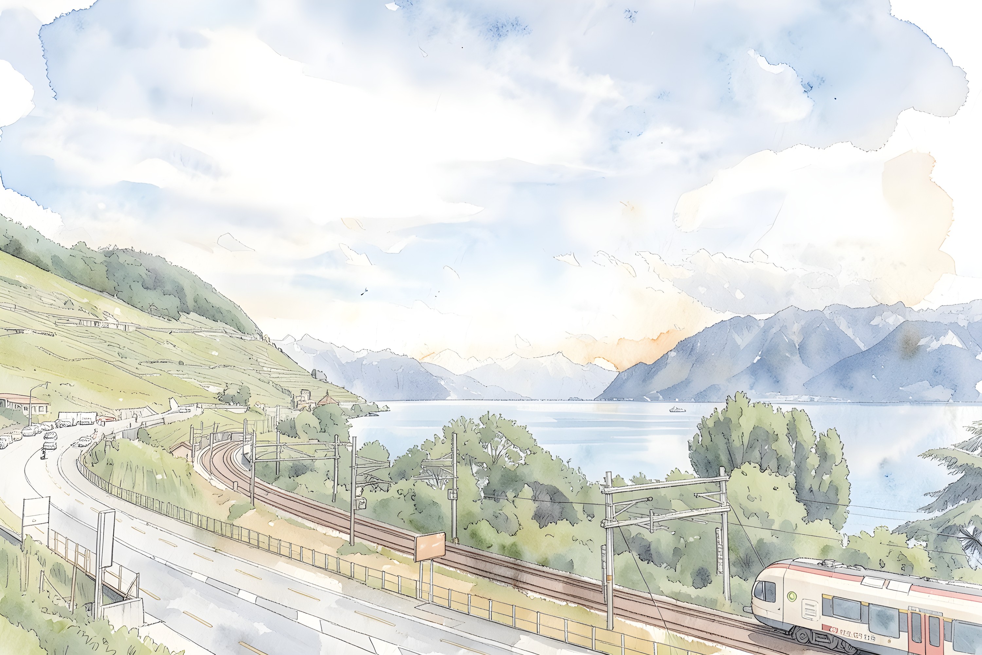
Photos/looks/_DSC7022-Enhanced-NR/12_watercolor.jpg
