adityuhkapoor/hack-mit-2026/Photos/looks/_DSC7022-Enhanced-NR/15_diorama.jpg

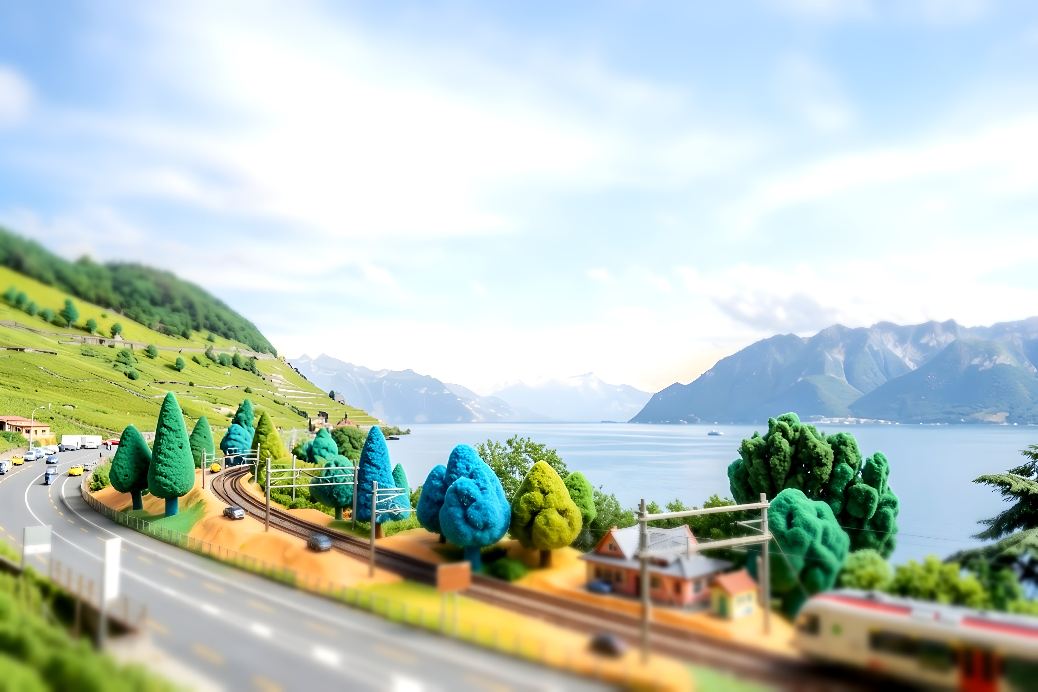
Photos/looks/_DSC7022-Enhanced-NR/15_diorama.jpg
