adityuhkapoor/hack-mit-2026/Photos/looks/_DSC8307-Enhanced-NR/00_original.jpg

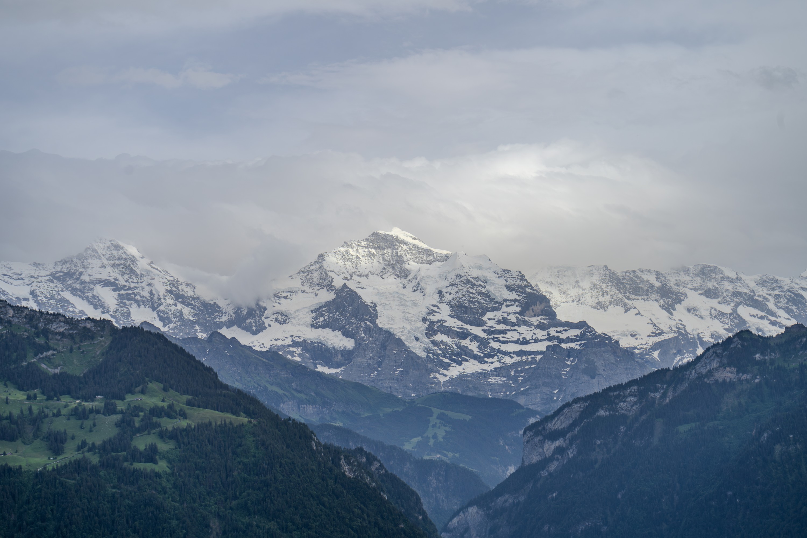
Photos/looks/_DSC8307-Enhanced-NR/00_original.jpg
