adityuhkapoor/hack-mit-2026/Photos/looks/_DSC8307-Enhanced-NR/06_digicam.jpg

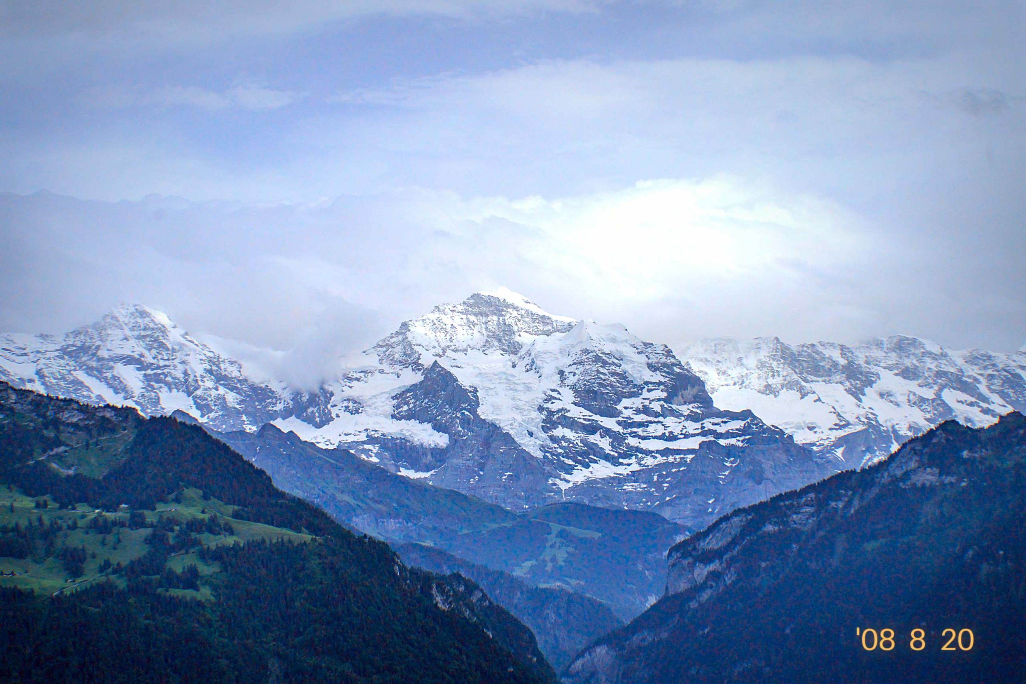
Photos/looks/_DSC8307-Enhanced-NR/06_digicam.jpg
