adityuhkapoor/hack-mit-2026/Photos/looks/_DSC8307-Enhanced-NR/08_instant.jpg

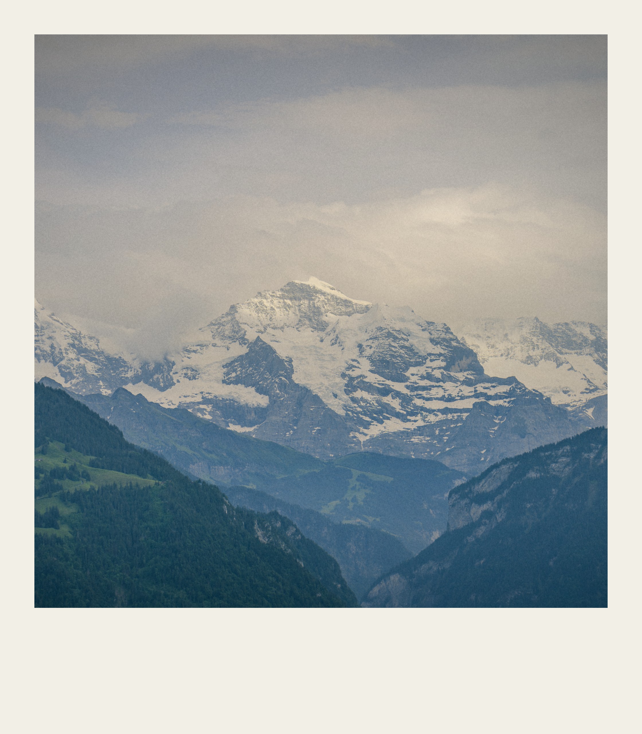
Photos/looks/_DSC8307-Enhanced-NR/08_instant.jpg
