adityuhkapoor/hack-mit-2026/Photos/looks/_DSC8307-Enhanced-NR/11_anime.jpg

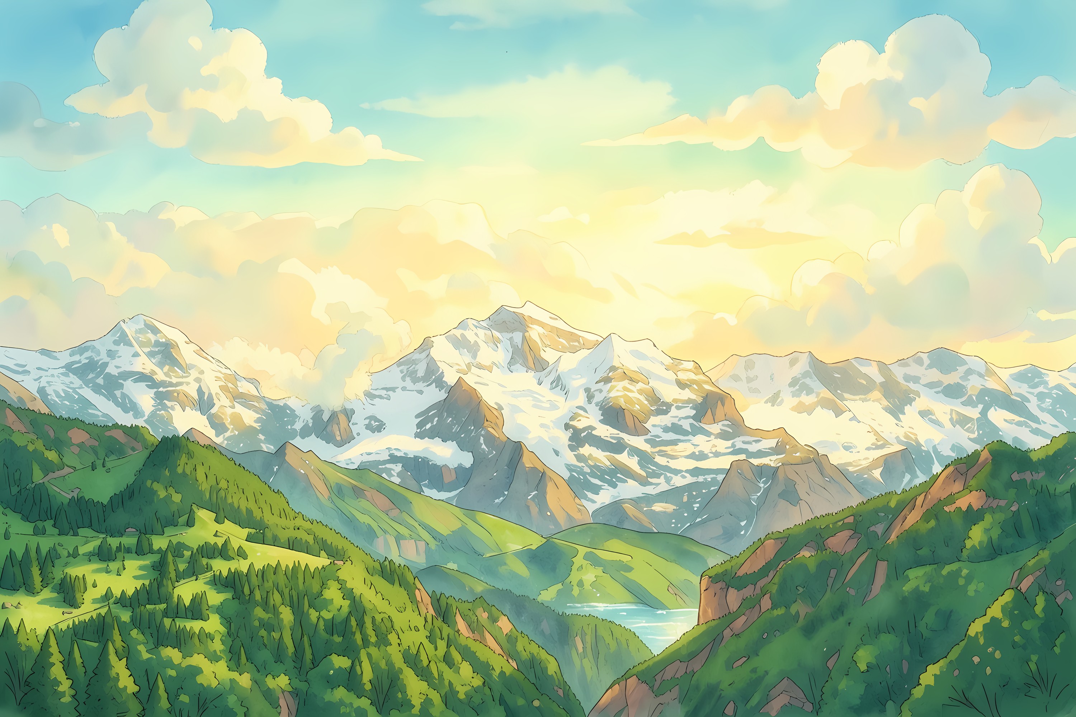
Photos/looks/_DSC8307-Enhanced-NR/11_anime.jpg
