adityuhkapoor/hack-mit-2026/Photos/looks/_DSC8307-Enhanced-NR/12_watercolor.jpg

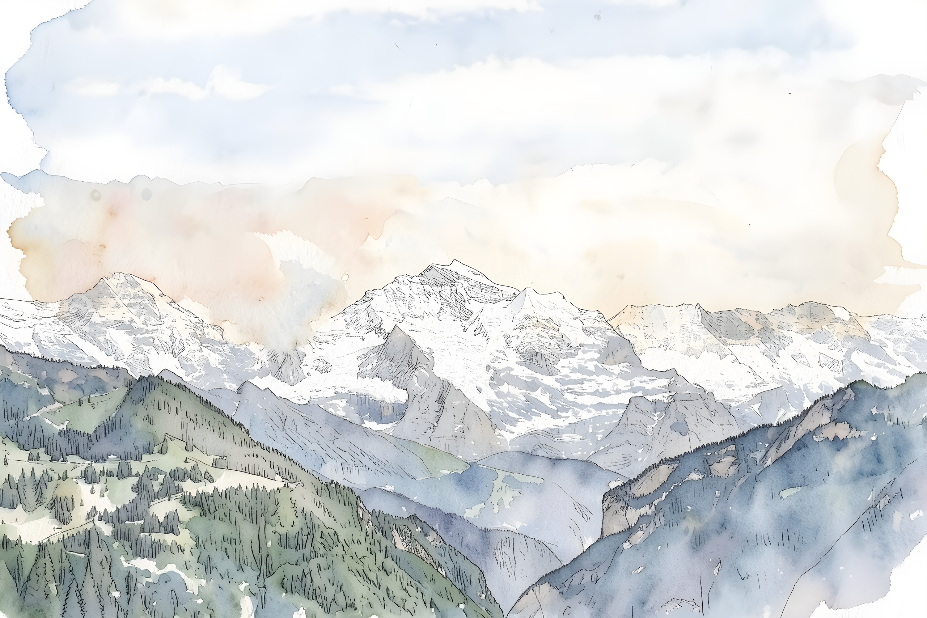
Photos/looks/_DSC8307-Enhanced-NR/12_watercolor.jpg
