adityuhkapoor/hack-mit-2026/Photos/looks/_DSC8307-Enhanced-NR/17_ref_faded_green.jpg

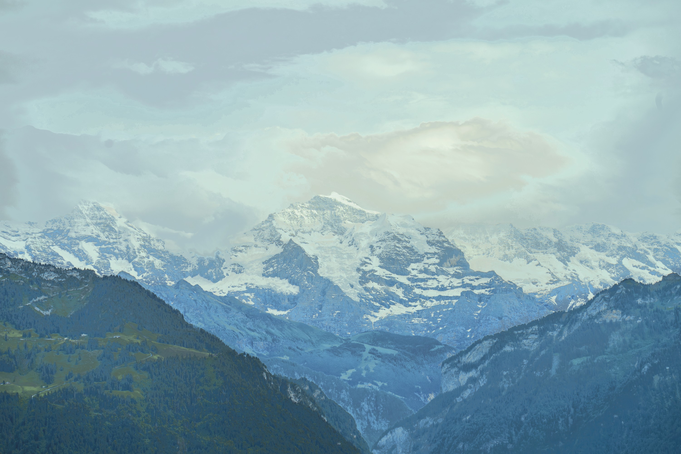
Photos/looks/_DSC8307-Enhanced-NR/17_ref_faded_green.jpg
