adityuhkapoor/hack-mit-2026/Photos/looks/_DSC8705-Enhanced-NR/01_velvia.jpg

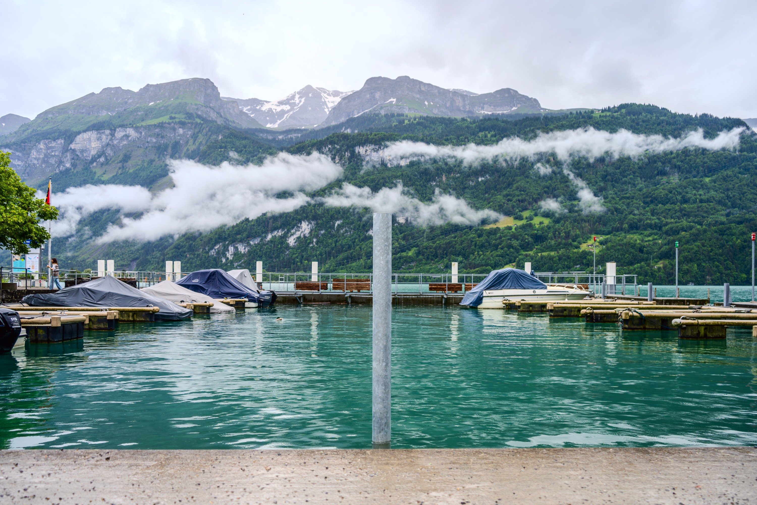
Photos/looks/_DSC8705-Enhanced-NR/01_velvia.jpg
