adityuhkapoor/hack-mit-2026/Photos/looks/_DSC8705-Enhanced-NR/03_teal_orange.jpg

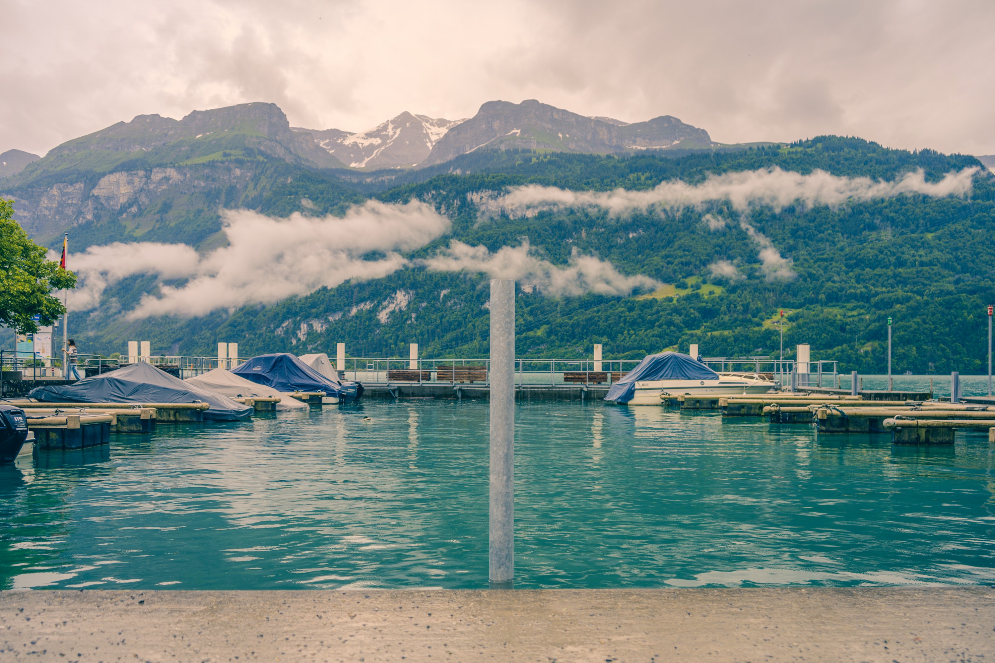
Photos/looks/_DSC8705-Enhanced-NR/03_teal_orange.jpg
