adityuhkapoor/hack-mit-2026/Photos/looks/_DSC8705-Enhanced-NR/06_digicam.jpg

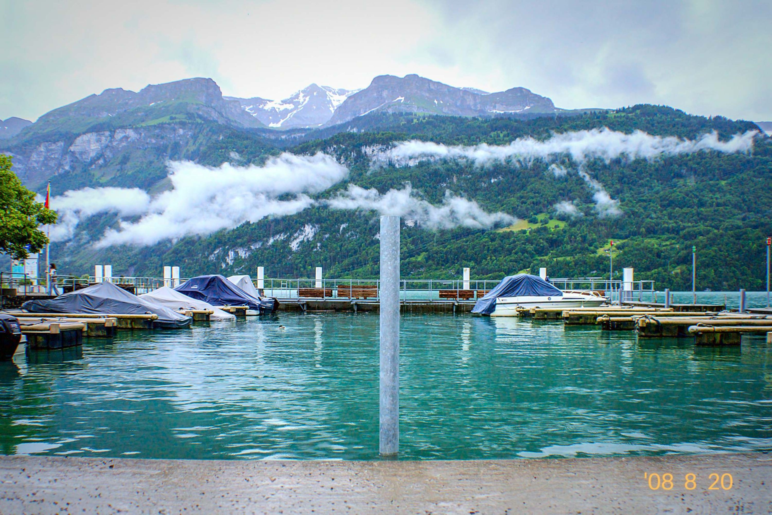
Photos/looks/_DSC8705-Enhanced-NR/06_digicam.jpg
