adityuhkapoor/hack-mit-2026/Photos/looks/_DSC8705-Enhanced-NR/08_instant.jpg

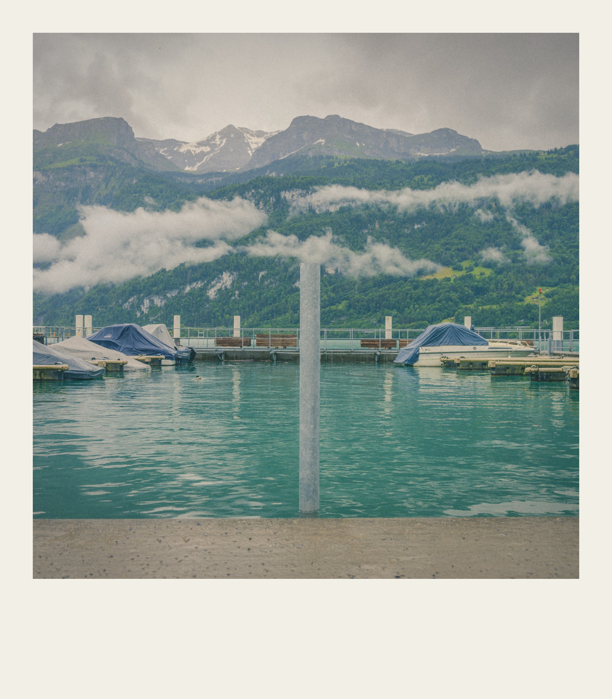
Photos/looks/_DSC8705-Enhanced-NR/08_instant.jpg
