adityuhkapoor/hack-mit-2026/Photos/looks/_DSC8705-Enhanced-NR/11_anime.jpg

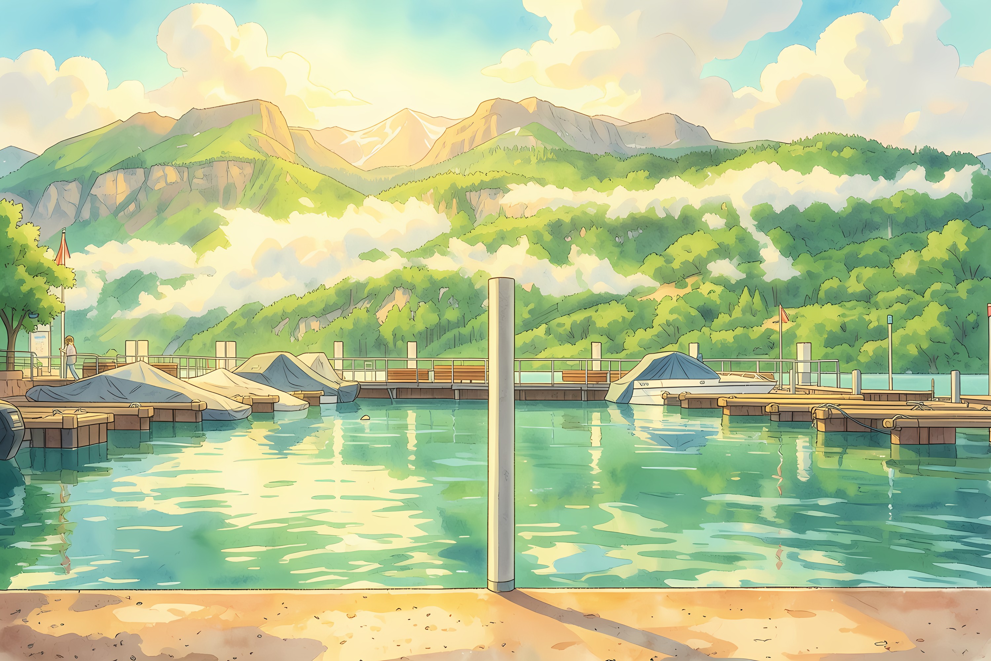
Photos/looks/_DSC8705-Enhanced-NR/11_anime.jpg
