adityuhkapoor/hack-mit-2026/Photos/looks/_DSC8705-Enhanced-NR/12_watercolor.jpg

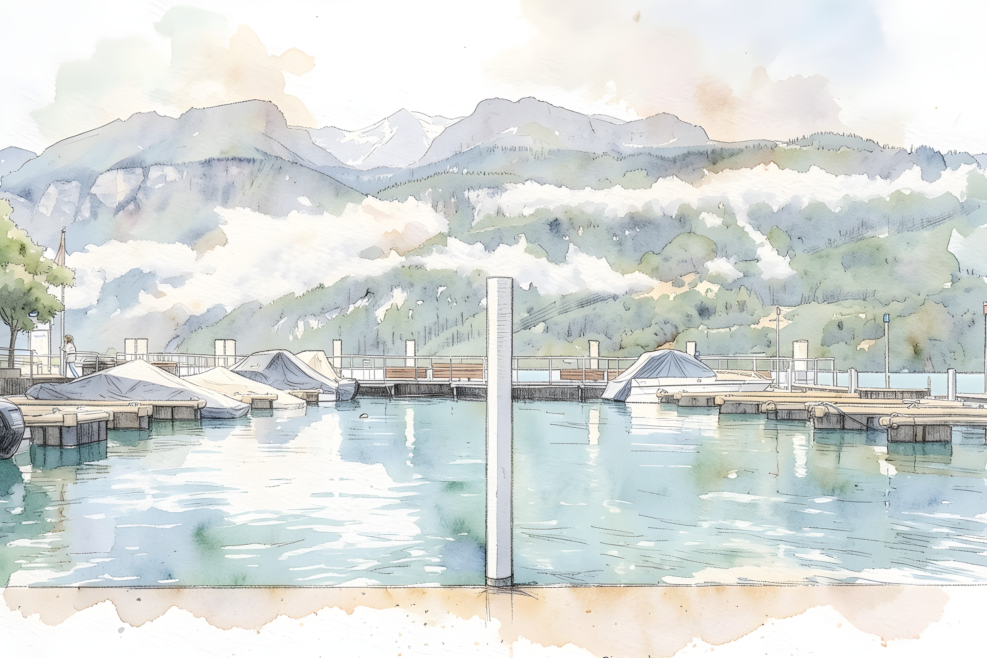
Photos/looks/_DSC8705-Enhanced-NR/12_watercolor.jpg
