adityuhkapoor/hack-mit-2026/Photos/looks/_DSC8705-Enhanced-NR/14_golden_hour.jpg

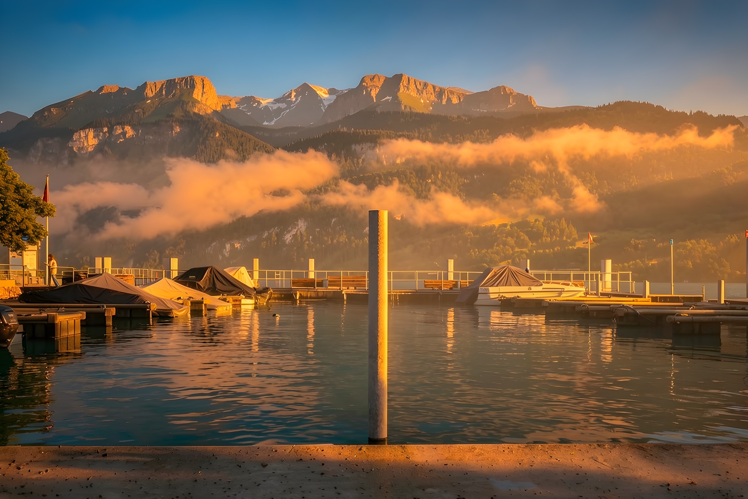
Photos/looks/_DSC8705-Enhanced-NR/14_golden_hour.jpg
