adityuhkapoor/hack-mit-2026/Photos/looks/_DSC8705-Enhanced-NR/15_diorama.jpg

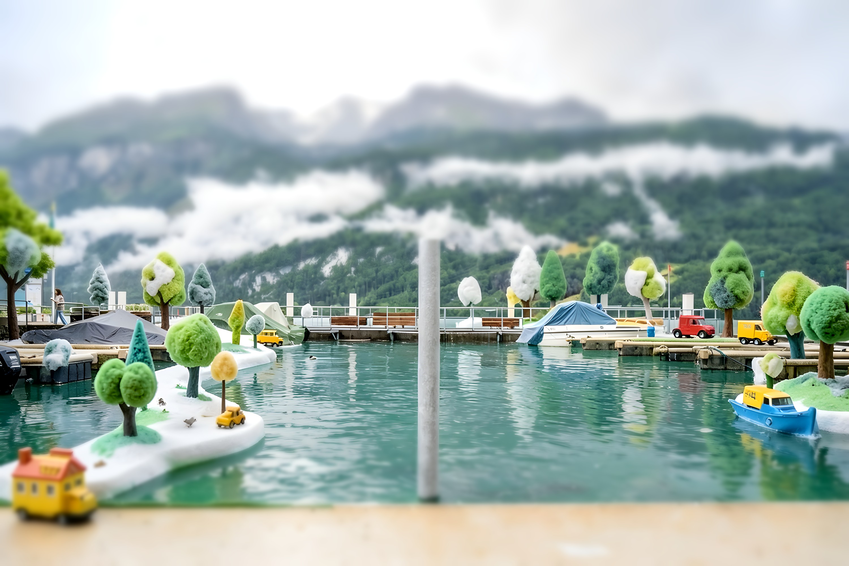
Photos/looks/_DSC8705-Enhanced-NR/15_diorama.jpg
