adityuhkapoor/hack-mit-2026/Photos/looks/_DSC8705-Enhanced-NR/16_ref_crossprocess.jpg

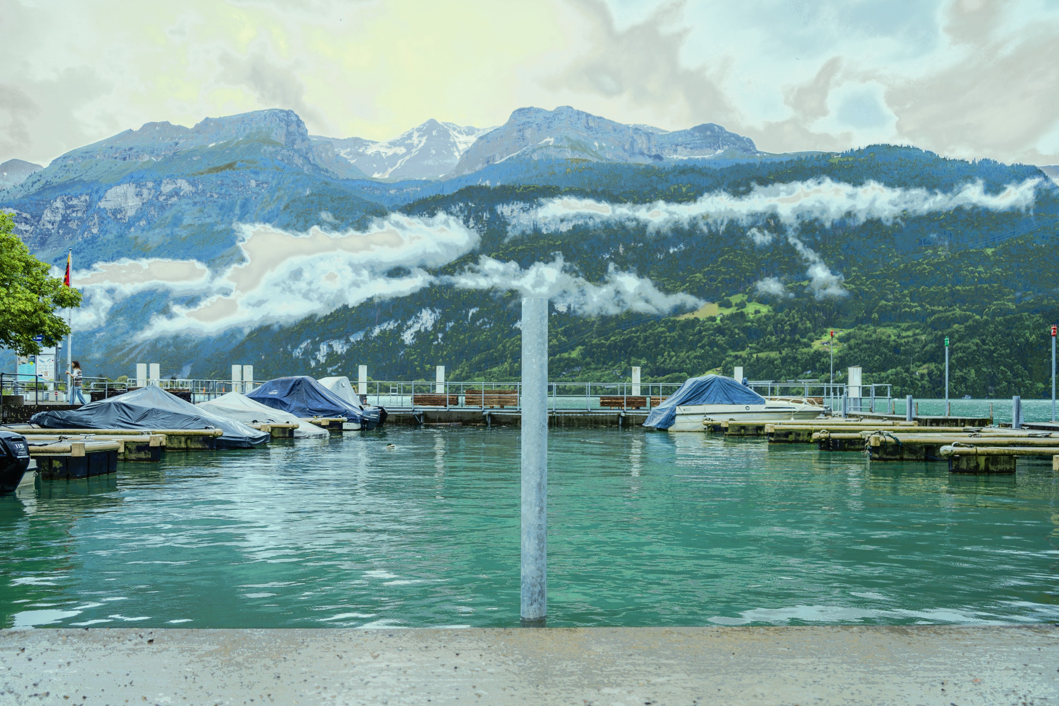
Photos/looks/_DSC8705-Enhanced-NR/16_ref_crossprocess.jpg
