adityuhkapoor/hack-mit-2026/Photos/looks/DSC00272-Enhanced-NR/01_velvia.jpg

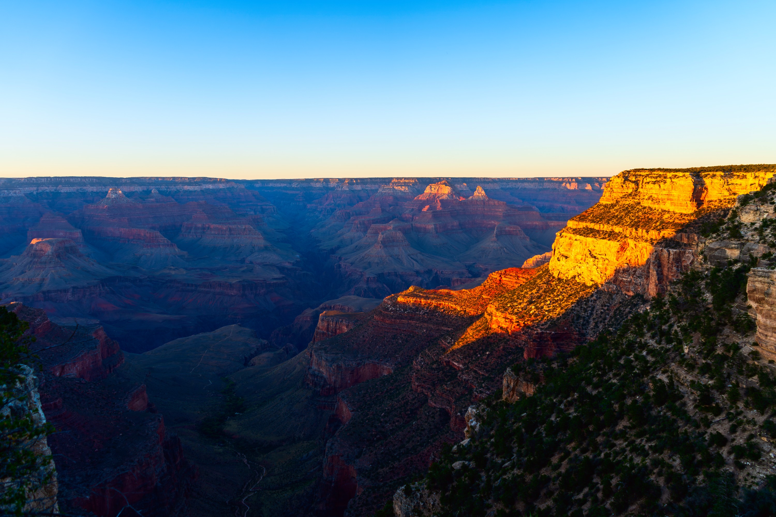
Photos/looks/DSC00272-Enhanced-NR/01_velvia.jpg
