adityuhkapoor/hack-mit-2026/Photos/looks/DSC00272-Enhanced-NR/06_digicam.jpg

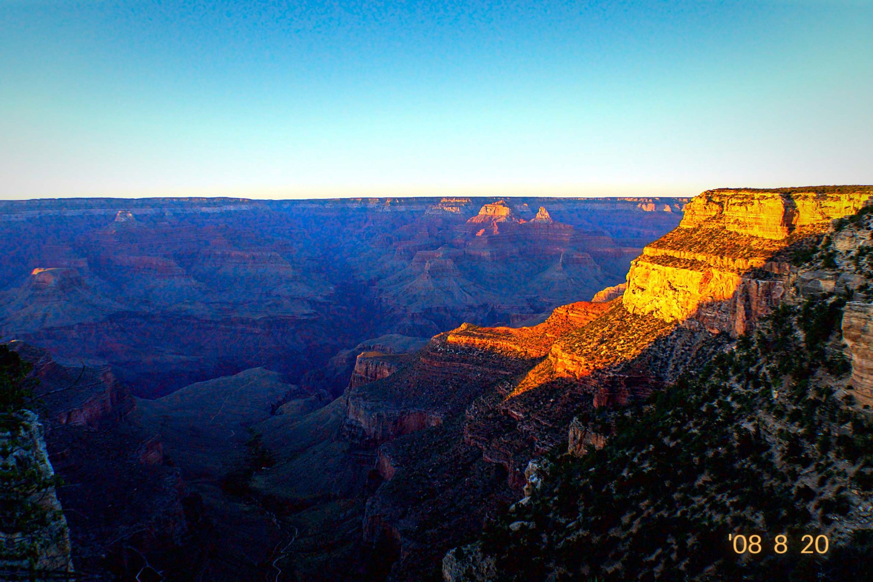
Photos/looks/DSC00272-Enhanced-NR/06_digicam.jpg
