adityuhkapoor/hack-mit-2026/Photos/looks/DSC00272-Enhanced-NR/08_instant.jpg

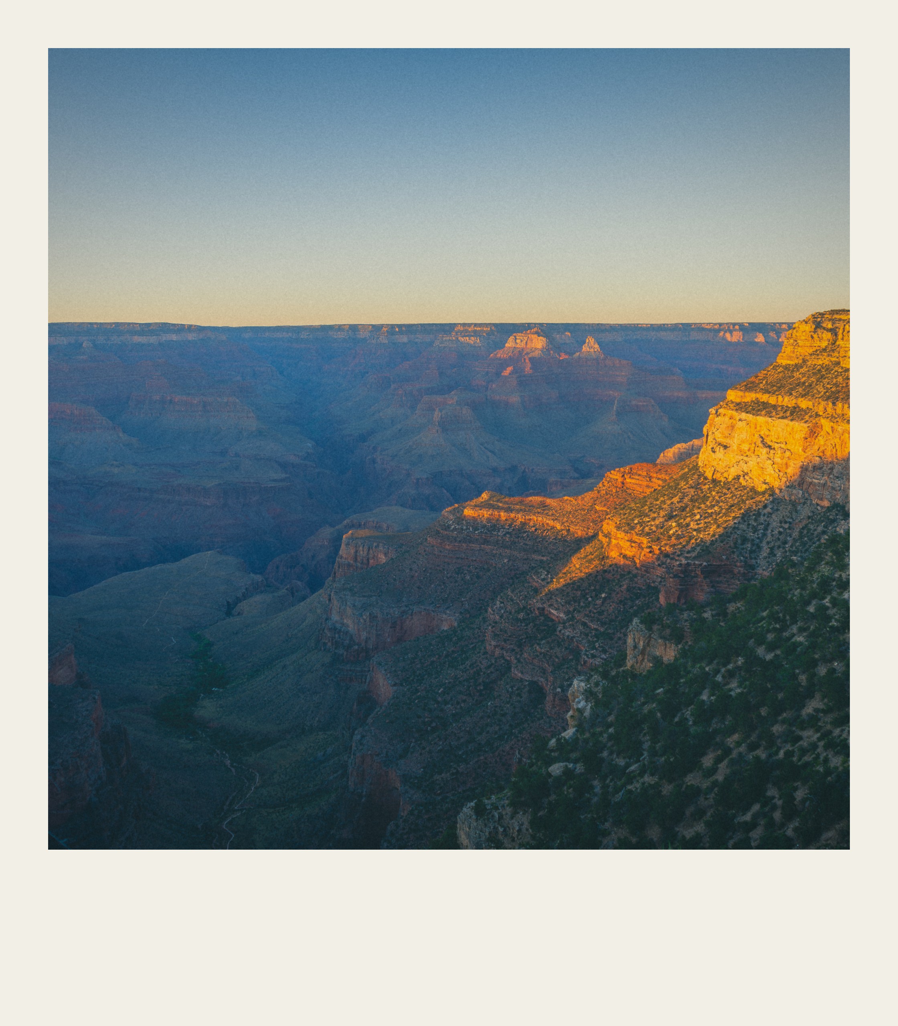
Photos/looks/DSC00272-Enhanced-NR/08_instant.jpg
