adityuhkapoor/hack-mit-2026/Photos/looks/DSC00272-Enhanced-NR/11_anime.jpg

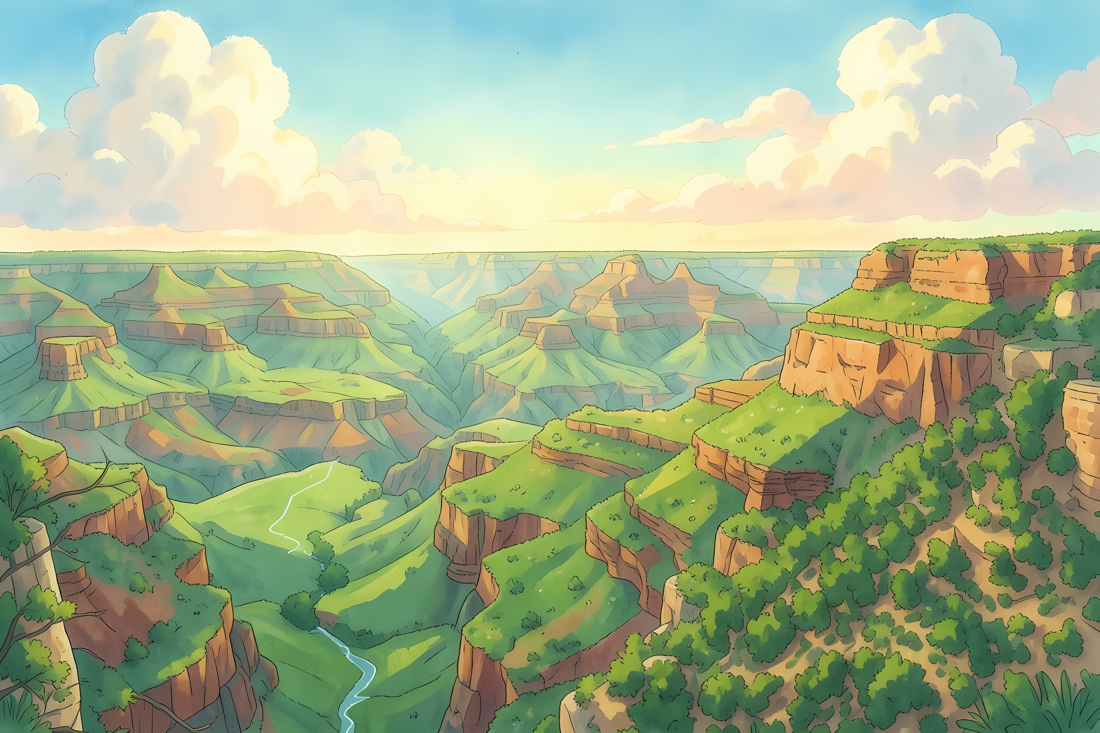
Photos/looks/DSC00272-Enhanced-NR/11_anime.jpg
