adityuhkapoor/hack-mit-2026/Photos/looks/DSC00272-Enhanced-NR/12_watercolor.jpg

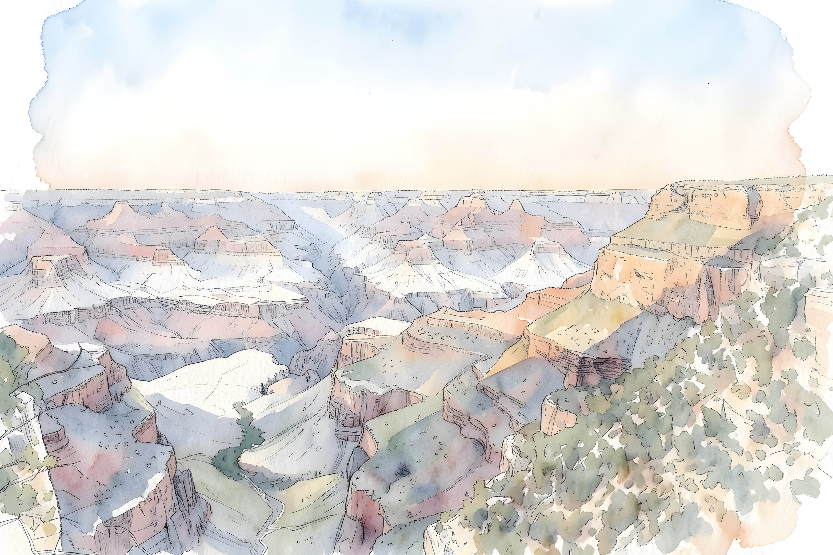
Photos/looks/DSC00272-Enhanced-NR/12_watercolor.jpg
