adityuhkapoor/hack-mit-2026/Photos/looks/DSC00272-Enhanced-NR/14_golden_hour.jpg

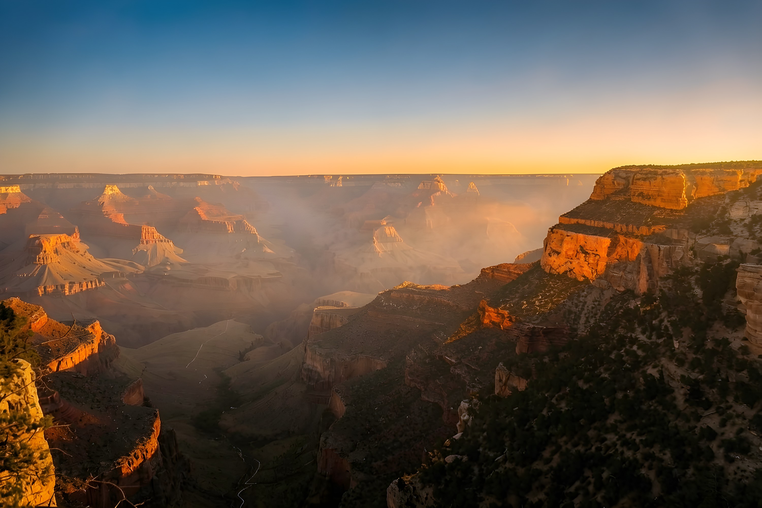
Photos/looks/DSC00272-Enhanced-NR/14_golden_hour.jpg
