adityuhkapoor/hack-mit-2026/Photos/looks/DSC00272-Enhanced-NR/15_diorama.jpg

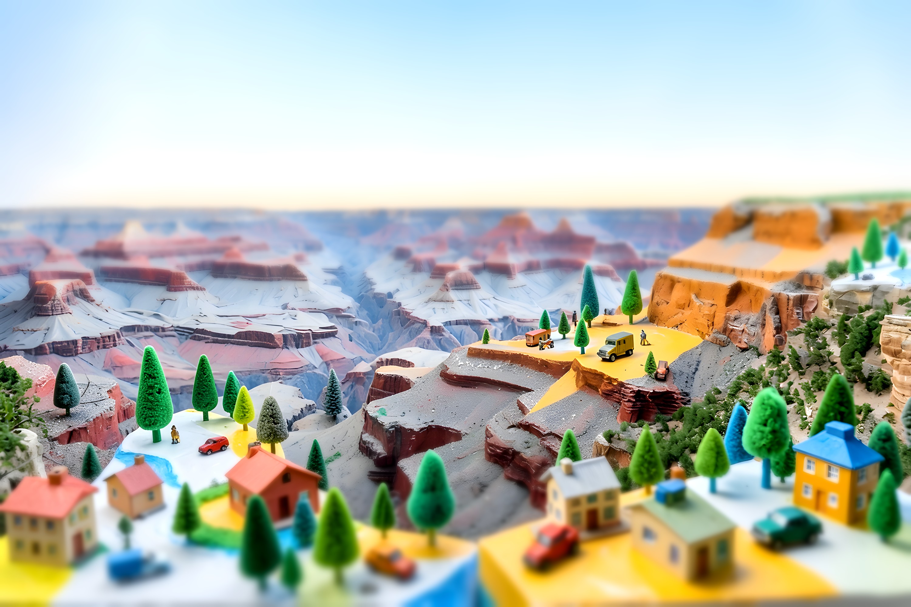
Photos/looks/DSC00272-Enhanced-NR/15_diorama.jpg
