adityuhkapoor/hack-mit-2026/Photos/looks/DSC00272-Enhanced-NR/16_ref_crossprocess.jpg

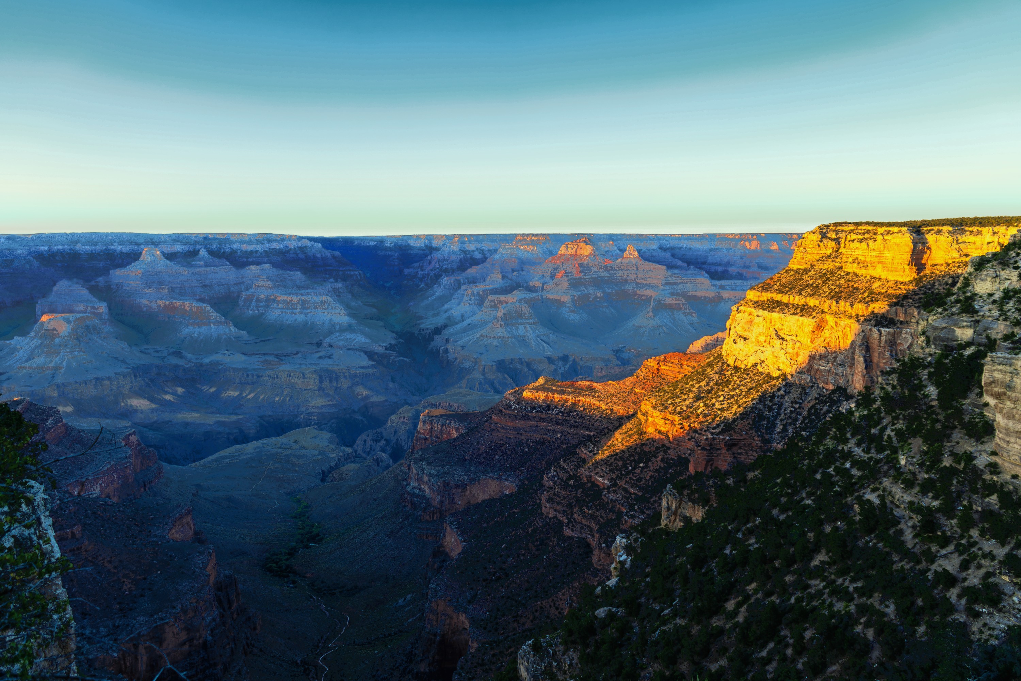
Photos/looks/DSC00272-Enhanced-NR/16_ref_crossprocess.jpg
