adityuhkapoor/hack-mit-2026/Photos/looks/DSC06684-Enhanced-NR/01_velvia.jpg

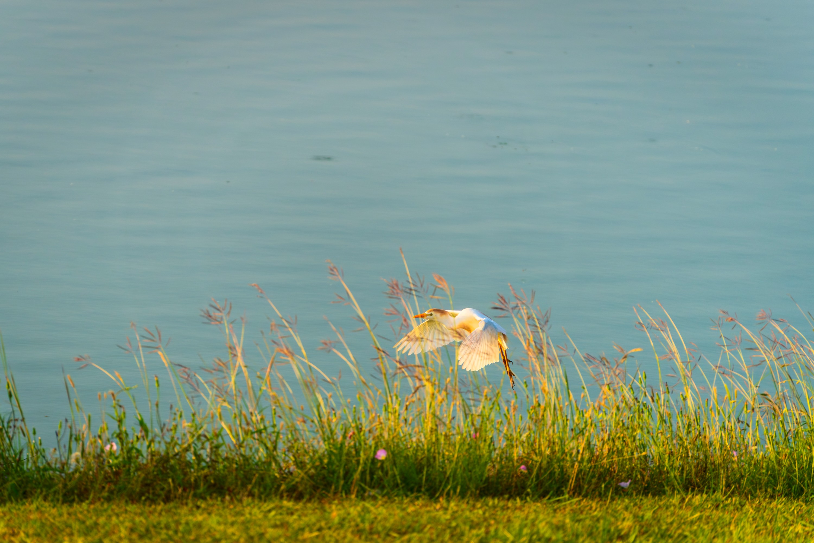
Photos/looks/DSC06684-Enhanced-NR/01_velvia.jpg
