adityuhkapoor/hack-mit-2026/Photos/looks/DSC06684-Enhanced-NR/04_faded_matte.jpg

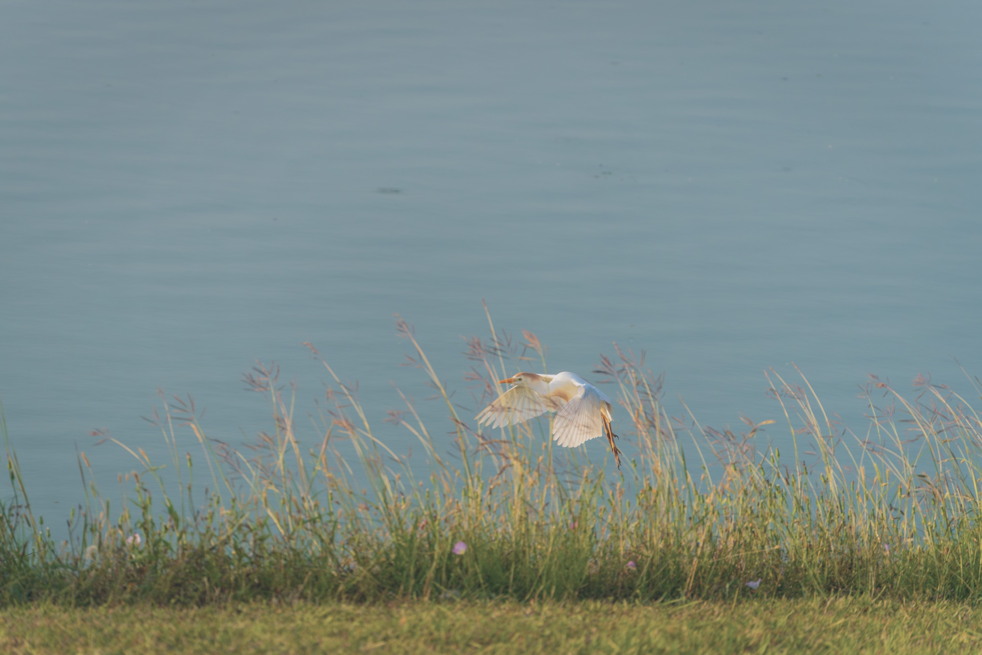
Photos/looks/DSC06684-Enhanced-NR/04_faded_matte.jpg
