adityuhkapoor/hack-mit-2026/Photos/looks/DSC06684-Enhanced-NR/05_mono.jpg

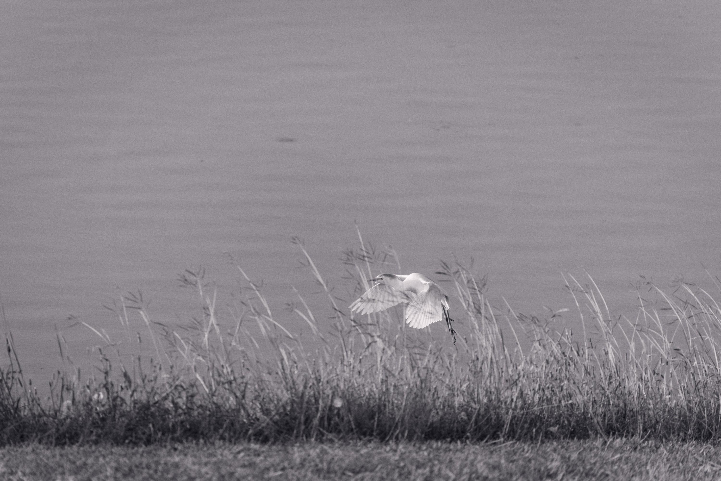
Photos/looks/DSC06684-Enhanced-NR/05_mono.jpg
