adityuhkapoor/hack-mit-2026/Photos/looks/DSC06684-Enhanced-NR/06_digicam.jpg

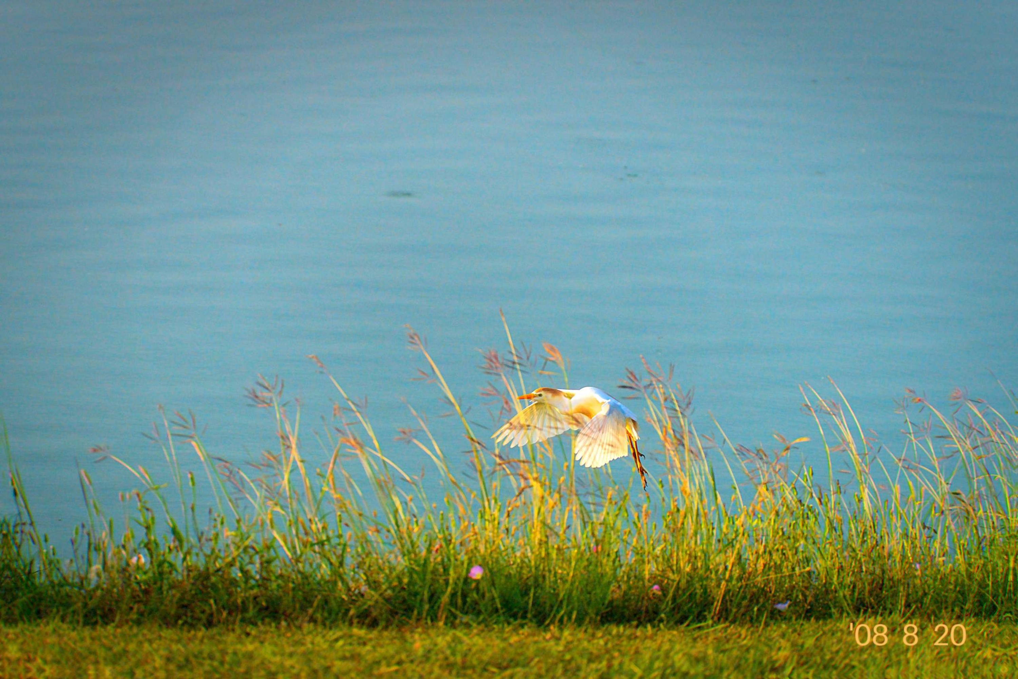
Photos/looks/DSC06684-Enhanced-NR/06_digicam.jpg
