adityuhkapoor/hack-mit-2026/Photos/looks/DSC06684-Enhanced-NR/07_cinestill.jpg

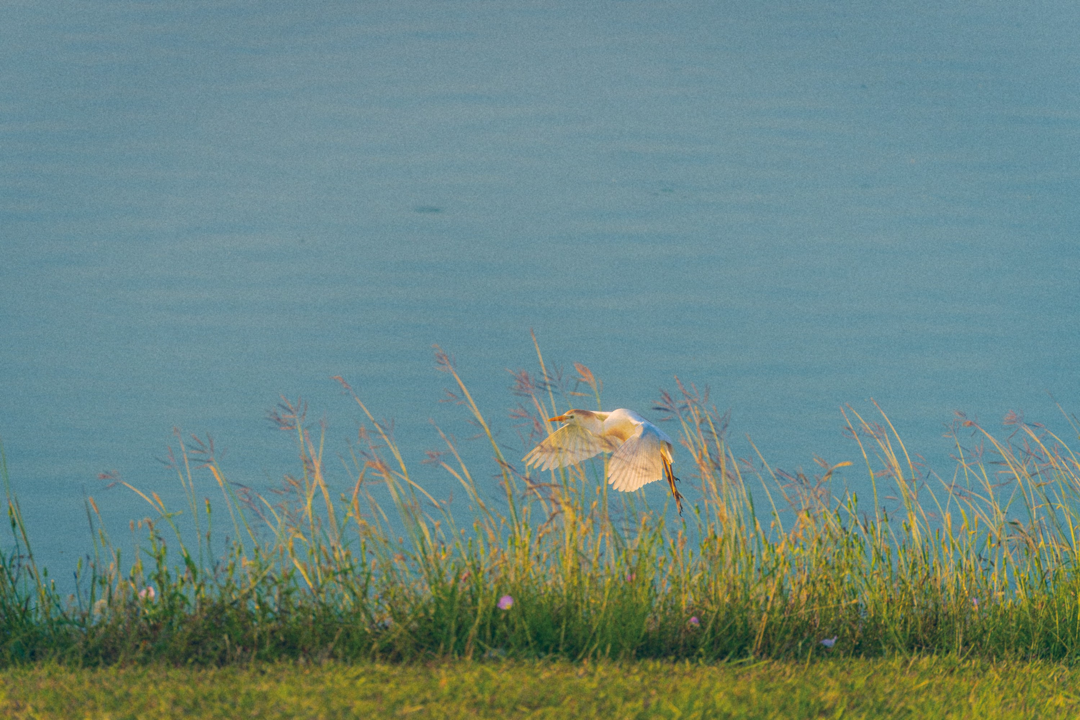
Photos/looks/DSC06684-Enhanced-NR/07_cinestill.jpg
