adityuhkapoor/hack-mit-2026/Photos/looks/DSC06684-Enhanced-NR/08_instant.jpg

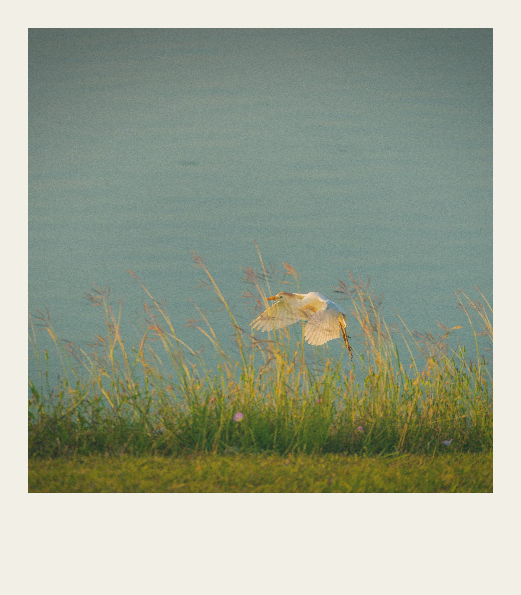
Photos/looks/DSC06684-Enhanced-NR/08_instant.jpg
