adityuhkapoor/hack-mit-2026/Photos/looks/DSC06684-Enhanced-NR/10_pixel.jpg

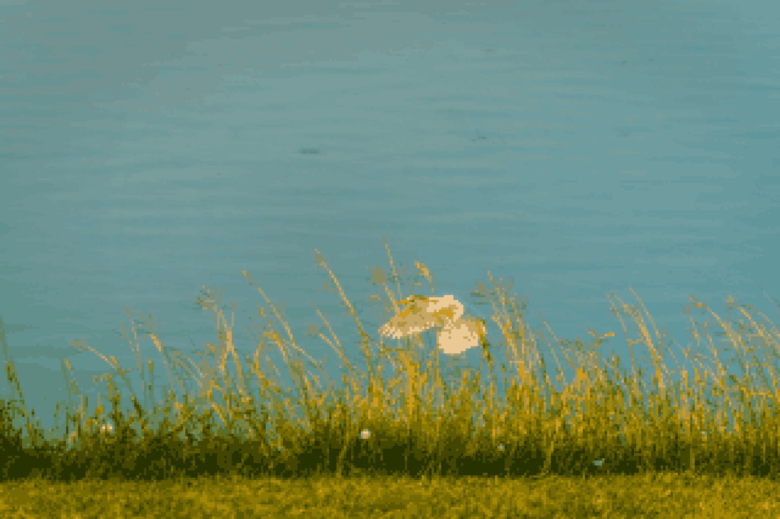
Photos/looks/DSC06684-Enhanced-NR/10_pixel.jpg
