adityuhkapoor/hack-mit-2026/Photos/looks/DSC06684-Enhanced-NR/11_anime.jpg

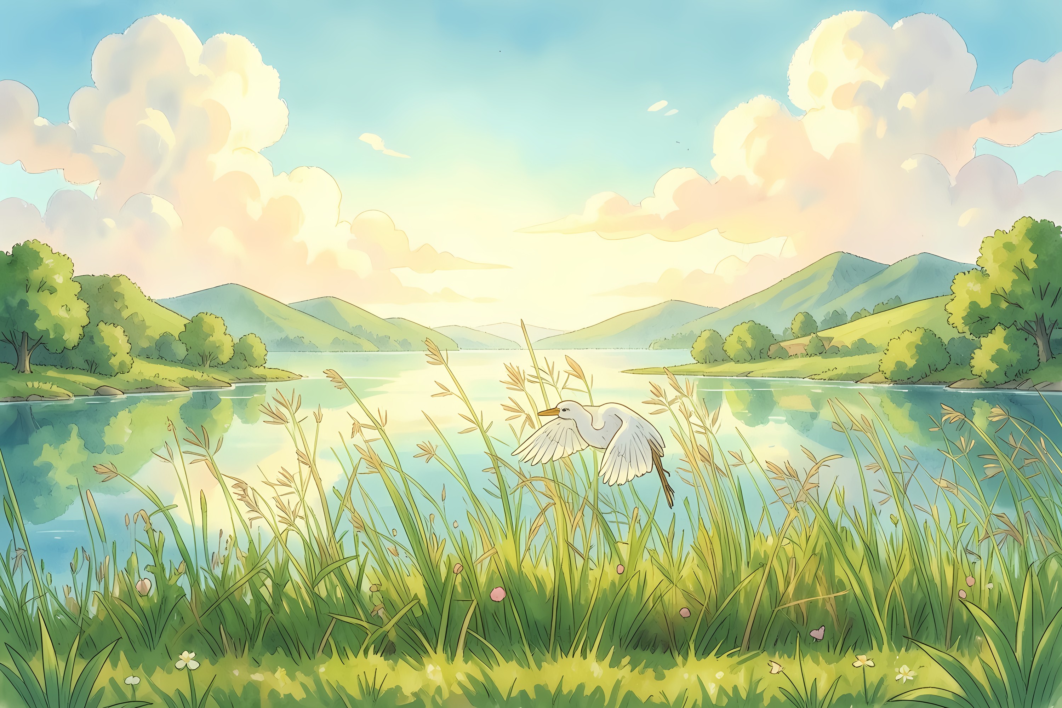
Photos/looks/DSC06684-Enhanced-NR/11_anime.jpg
