adityuhkapoor/hack-mit-2026/Photos/looks/DSC06684-Enhanced-NR/12_watercolor.jpg

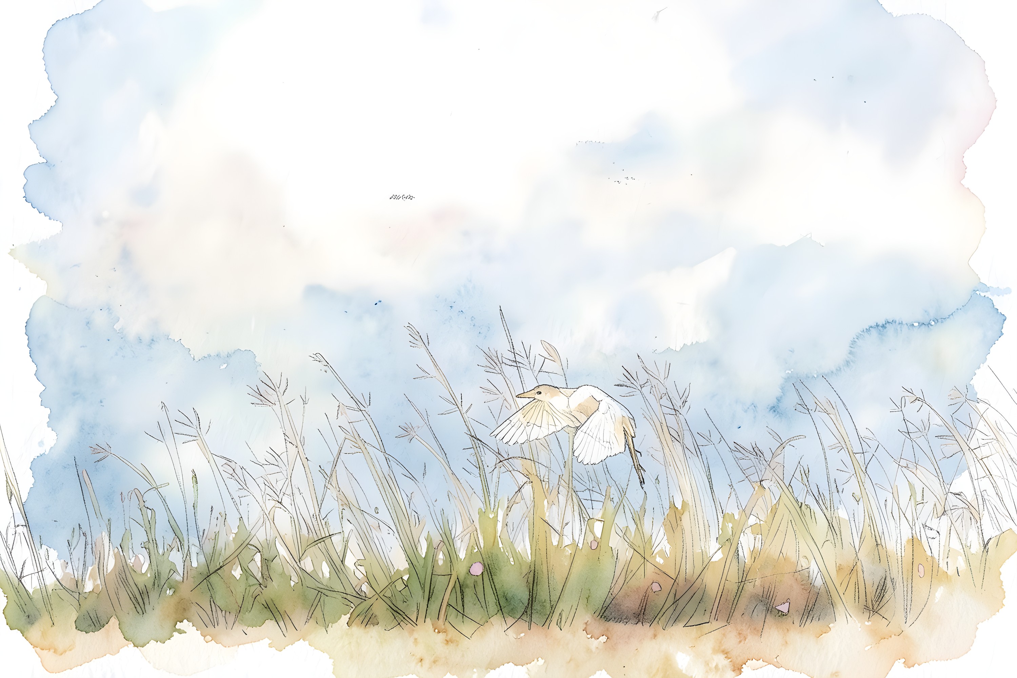
Photos/looks/DSC06684-Enhanced-NR/12_watercolor.jpg
