adityuhkapoor/hack-mit-2026/Photos/looks/DSC06684-Enhanced-NR/14_golden_hour.jpg

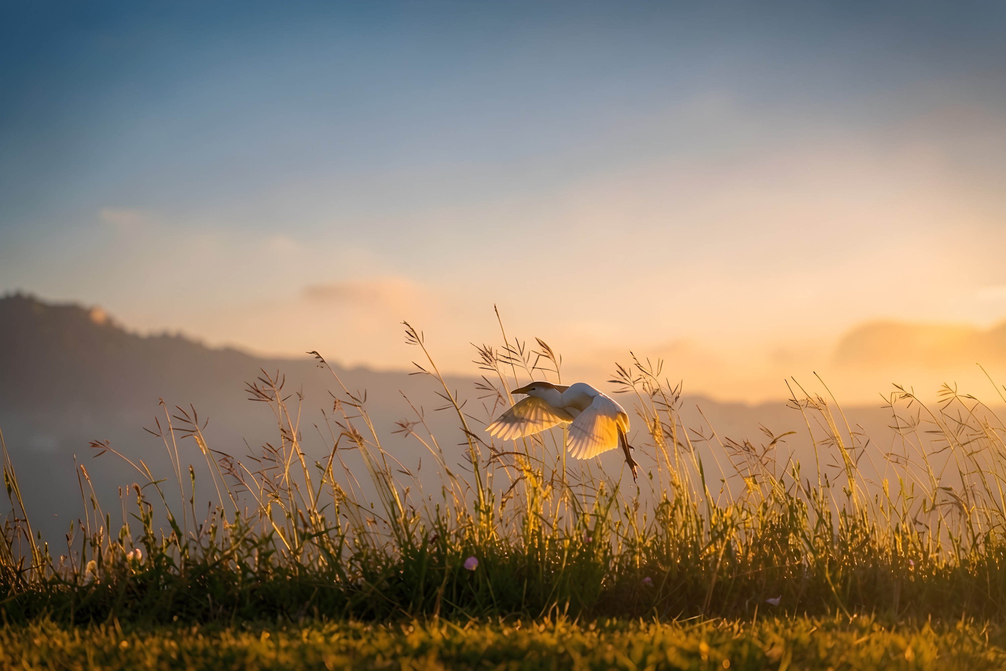
Photos/looks/DSC06684-Enhanced-NR/14_golden_hour.jpg
