adityuhkapoor/hack-mit-2026/Photos/looks/DSC06684-Enhanced-NR/15_diorama.jpg

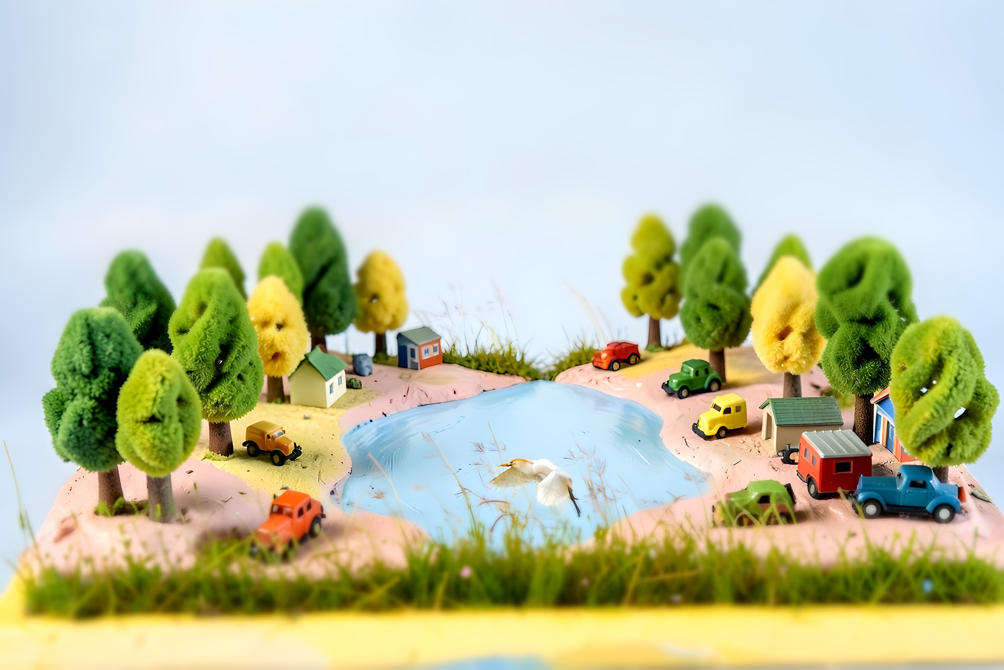
Photos/looks/DSC06684-Enhanced-NR/15_diorama.jpg
