adityuhkapoor/hack-mit-2026/Photos/looks/DSC06684-Enhanced-NR/16_ref_crossprocess.jpg

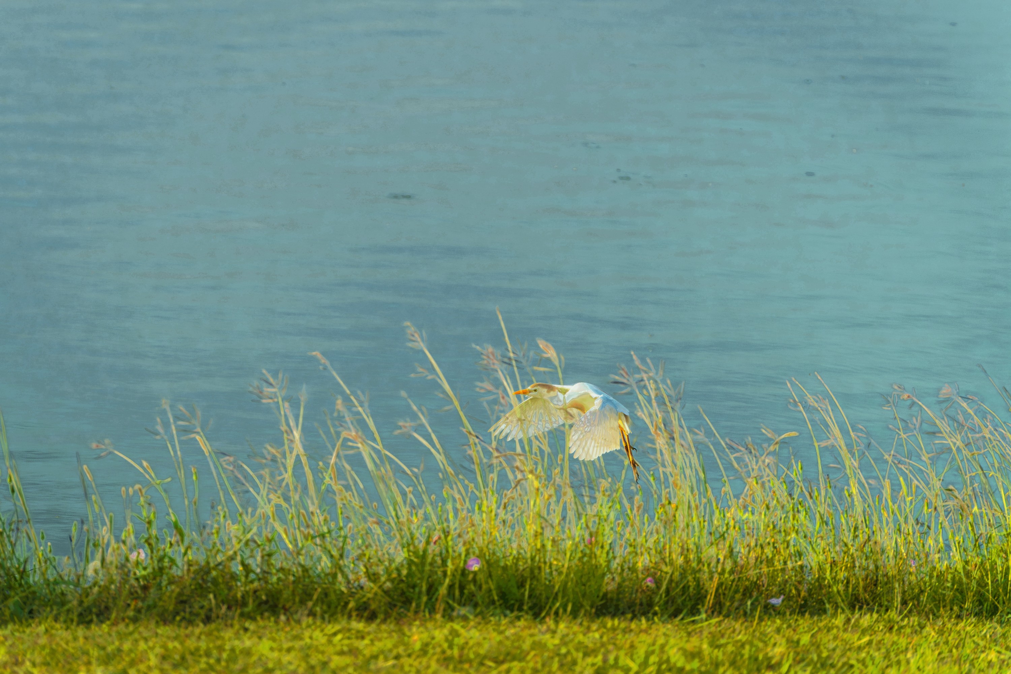
Photos/looks/DSC06684-Enhanced-NR/16_ref_crossprocess.jpg
