adityuhkapoor/hack-mit-2026/Photos/looks/DSC06684-Enhanced-NR/18_ref_sepia.jpg

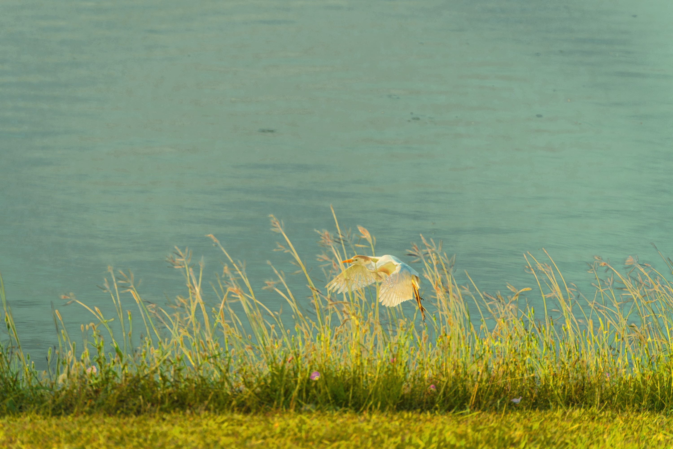
Photos/looks/DSC06684-Enhanced-NR/18_ref_sepia.jpg
