adityuhkapoor/hack-mit-2026/Photos/looks/IMG_0223/00_original.jpg

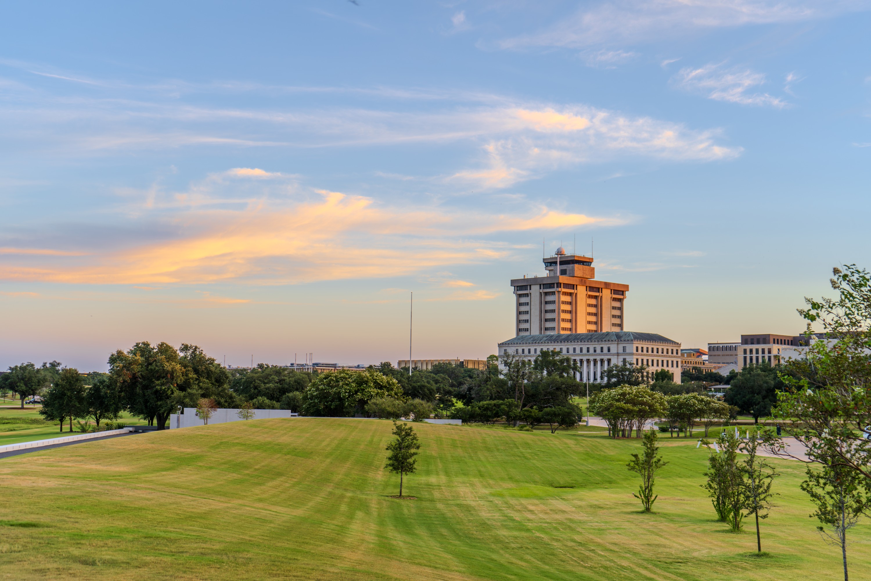
Photos/looks/IMG_0223/00_original.jpg
