adityuhkapoor/hack-mit-2026/Photos/looks/IMG_0223/01_velvia.jpg

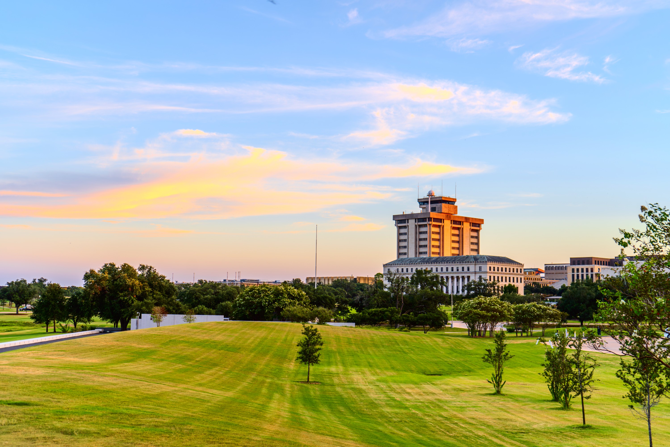
Photos/looks/IMG_0223/01_velvia.jpg
