adityuhkapoor/hack-mit-2026/Photos/looks/IMG_0223/06_digicam.jpg

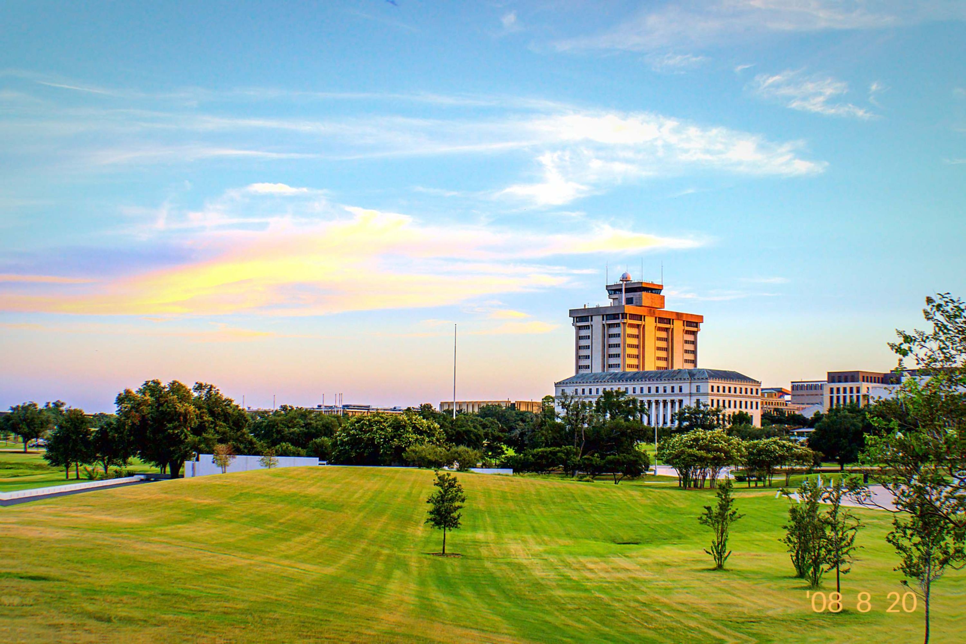
Photos/looks/IMG_0223/06_digicam.jpg
