adityuhkapoor/hack-mit-2026/Photos/looks/IMG_0223/08_instant.jpg

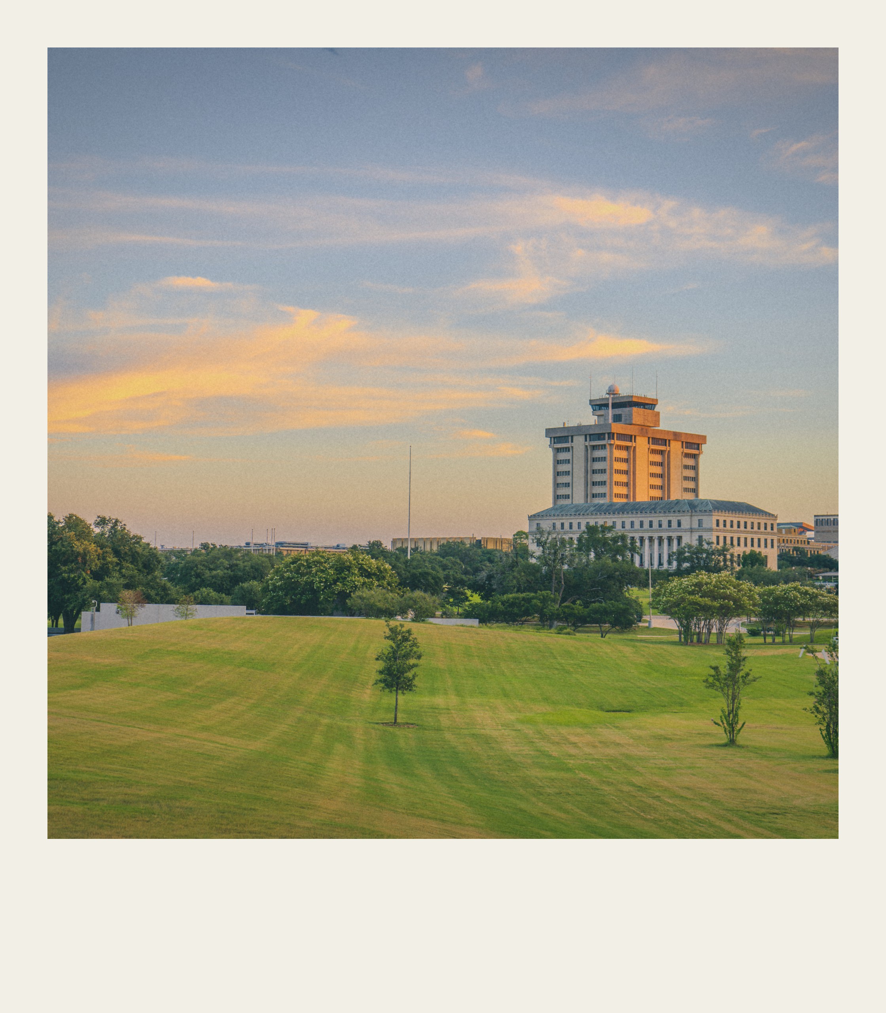
Photos/looks/IMG_0223/08_instant.jpg
