adityuhkapoor/hack-mit-2026/Photos/looks/IMG_0223/11_anime.jpg

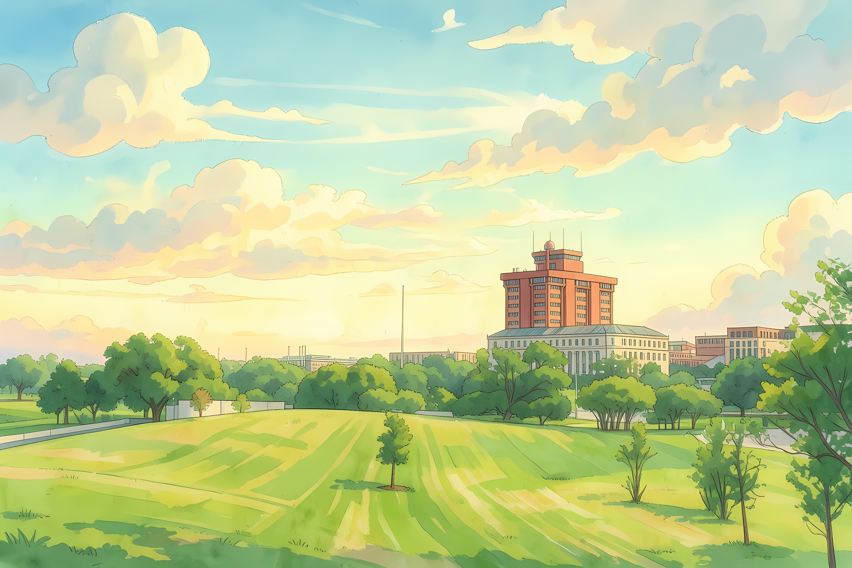
Photos/looks/IMG_0223/11_anime.jpg
