adityuhkapoor/hack-mit-2026/Photos/looks/IMG_0223/12_watercolor.jpg

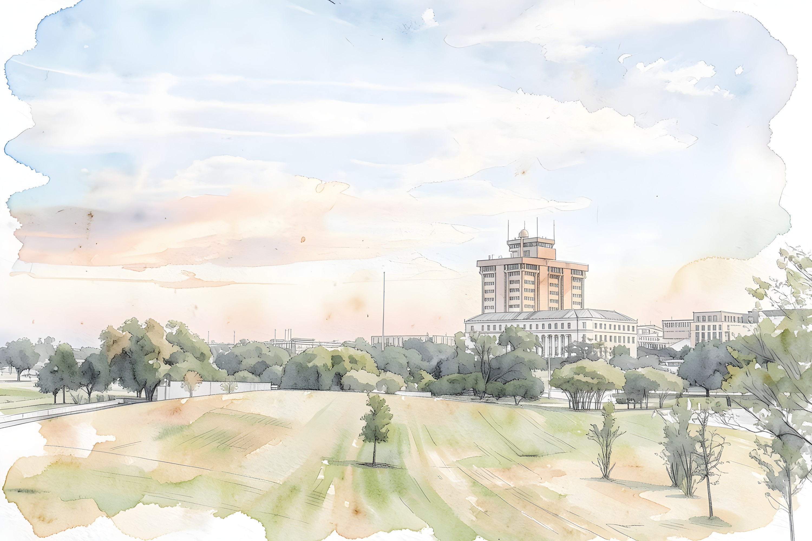
Photos/looks/IMG_0223/12_watercolor.jpg
