adityuhkapoor/hack-mit-2026/Photos/looks/IMG_0223/14_golden_hour.jpg

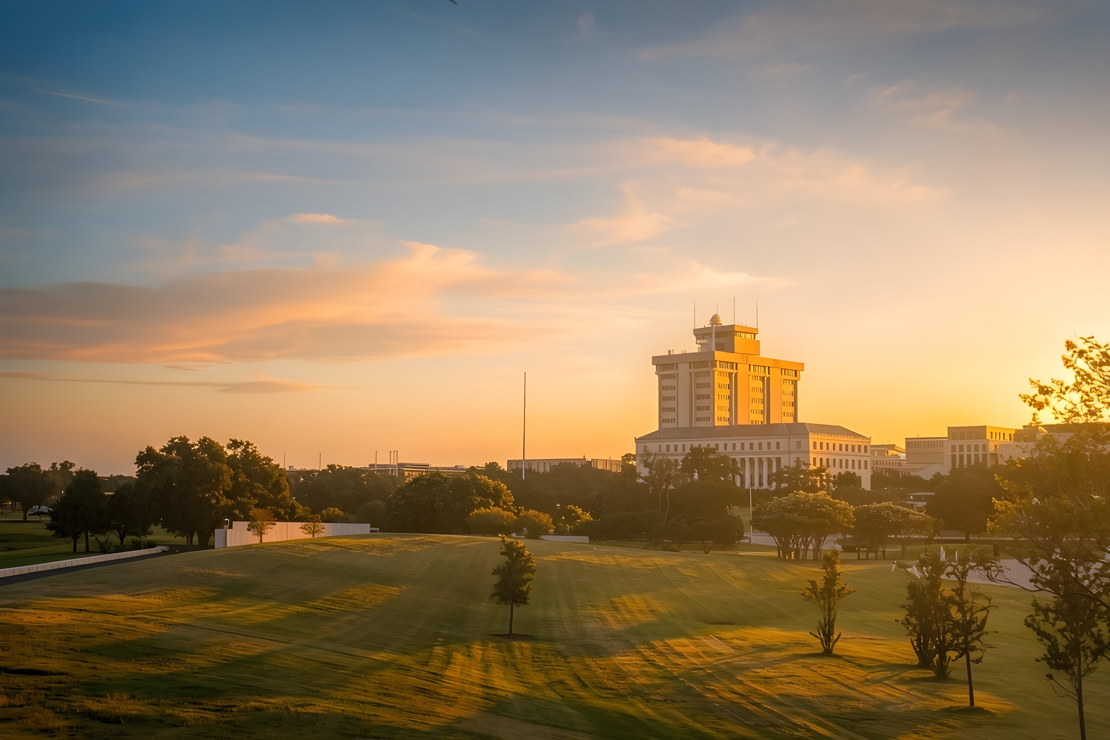
Photos/looks/IMG_0223/14_golden_hour.jpg
