adityuhkapoor/hack-mit-2026/Photos/looks/IMG_0223/15_diorama.jpg

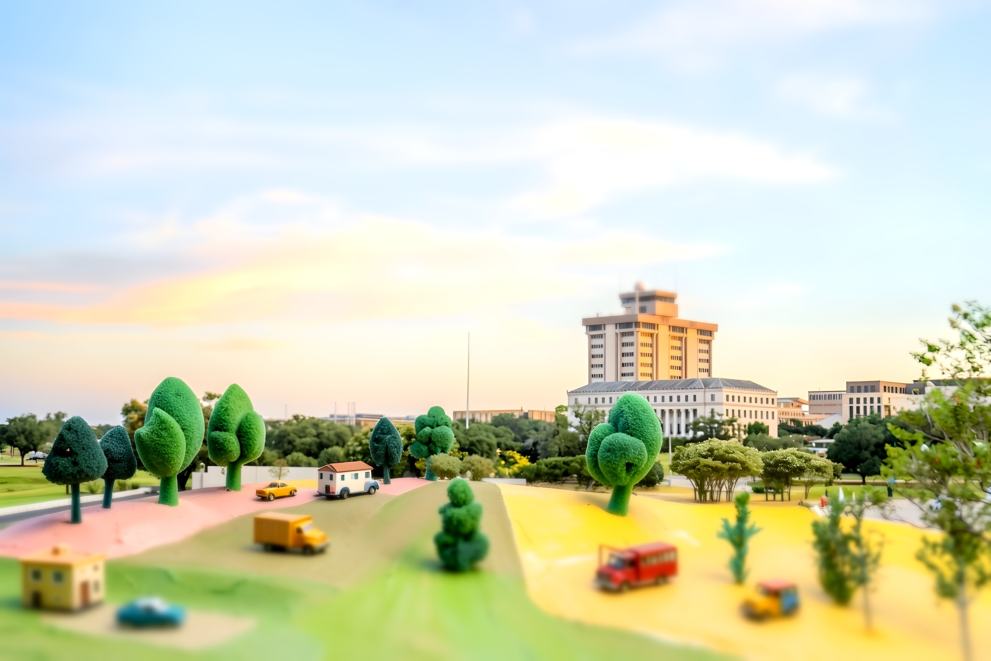
Photos/looks/IMG_0223/15_diorama.jpg
