adityuhkapoor/hack-mit-2026/Photos/looks/IMG_0223/16_ref_crossprocess.jpg

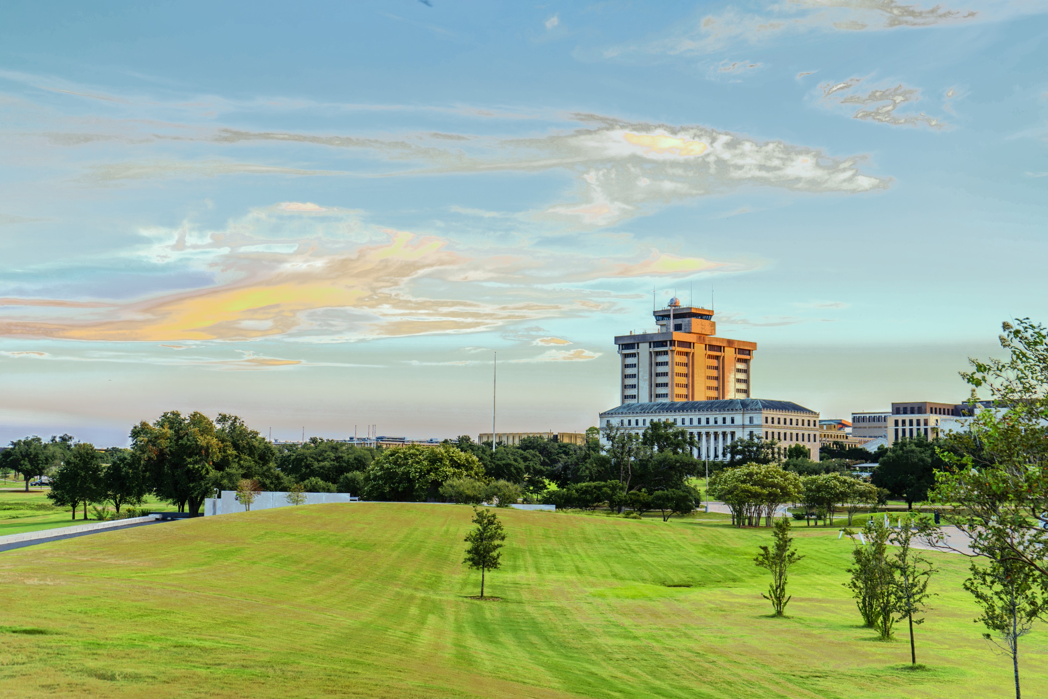
Photos/looks/IMG_0223/16_ref_crossprocess.jpg
