adityuhkapoor/hack-mit-2026/pipeline/nimbus/data/hackmit_caption.png

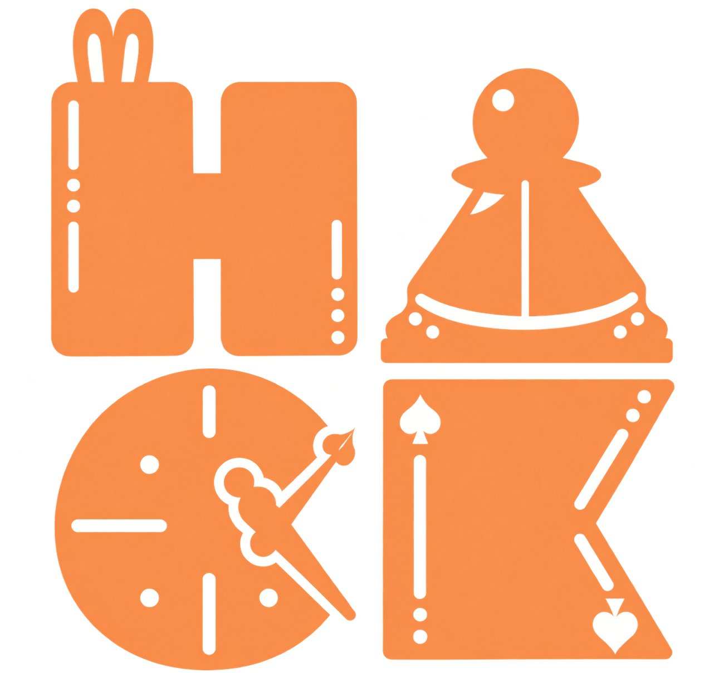
pipeline/nimbus/data/hackmit_caption.png
