adityuhkapoor/hack-mit-2026/pipeline/nimbus/data/polaroid_frame.png

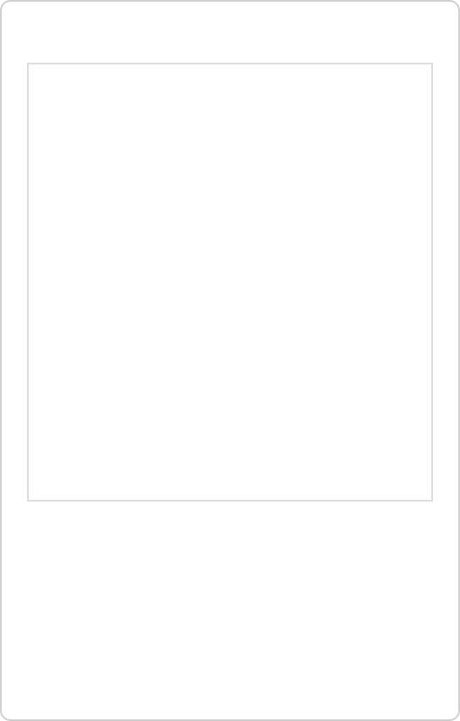
pipeline/nimbus/data/polaroid_frame.png
