adityuhkapoor/hack-mit-2026/pipeline/nimbus/data/polaroid_frame_full.png

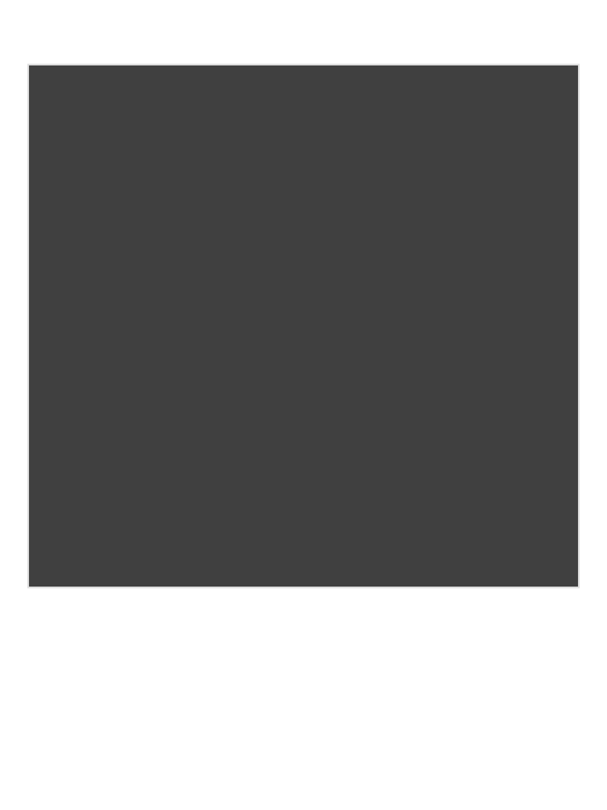
pipeline/nimbus/data/polaroid_frame_full.png
