adityuhkapoor/hack-mit-2026/Sponsor Tracks/IMG_1972.jpeg

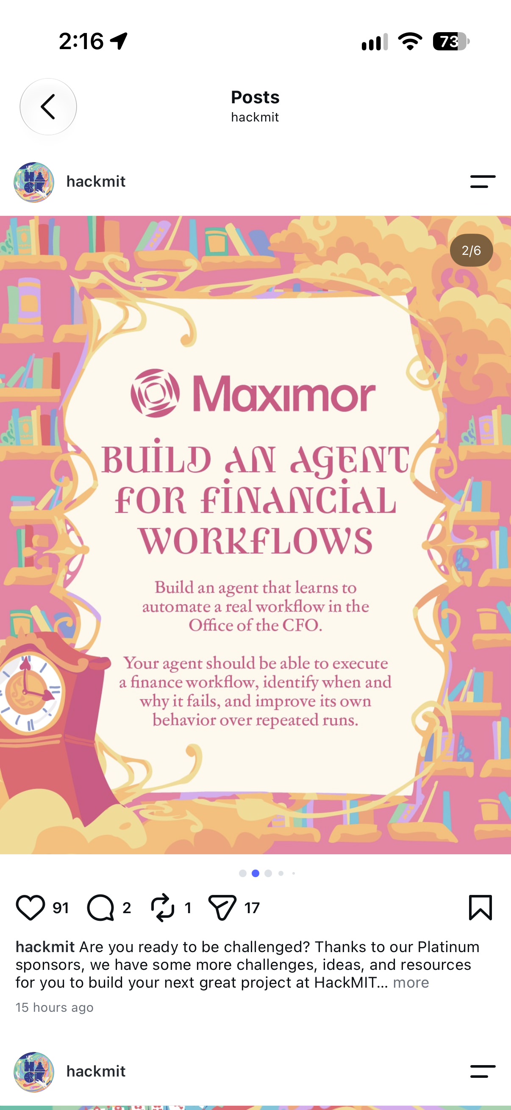
Sponsor Tracks/IMG_1972.jpeg
