adityuhkapoor/hack-mit-2026/Sponsor Tracks/IMG_1973.jpeg

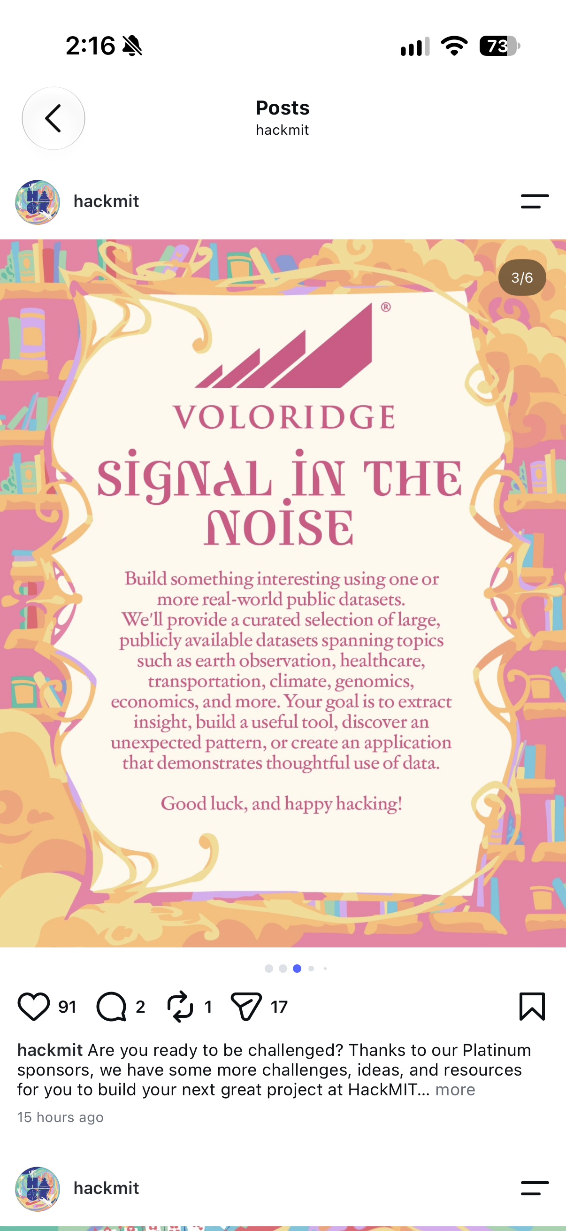
Sponsor Tracks/IMG_1973.jpeg
