adityuhkapoor/hack-mit-2026/Sponsor Tracks/IMG_1974.jpeg

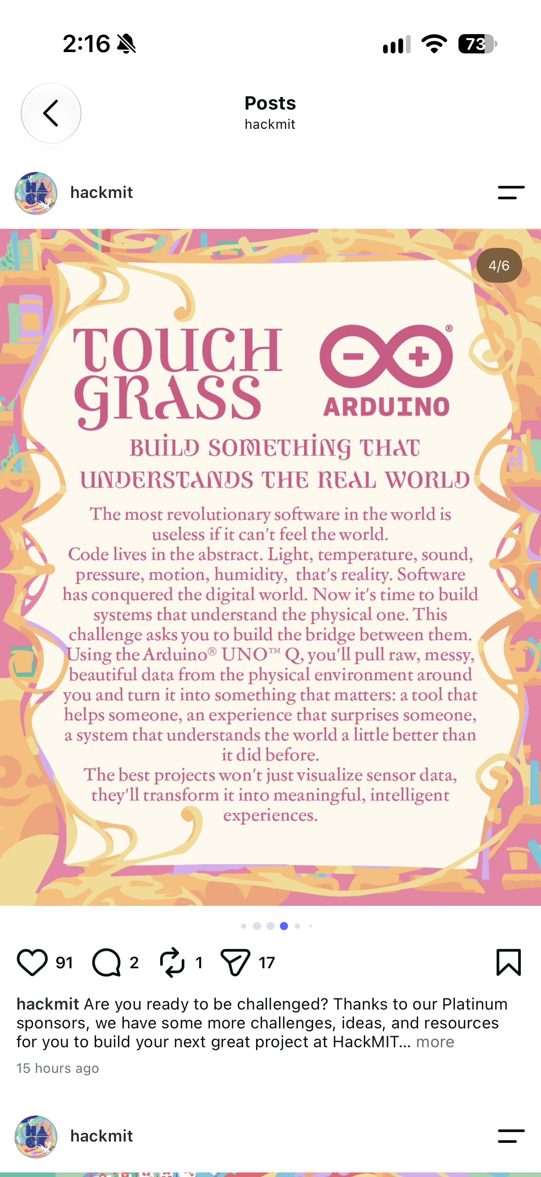
Sponsor Tracks/IMG_1974.jpeg
