adityuhkapoor/hack-mit-2026/Sponsor Tracks/IMG_1975.jpeg

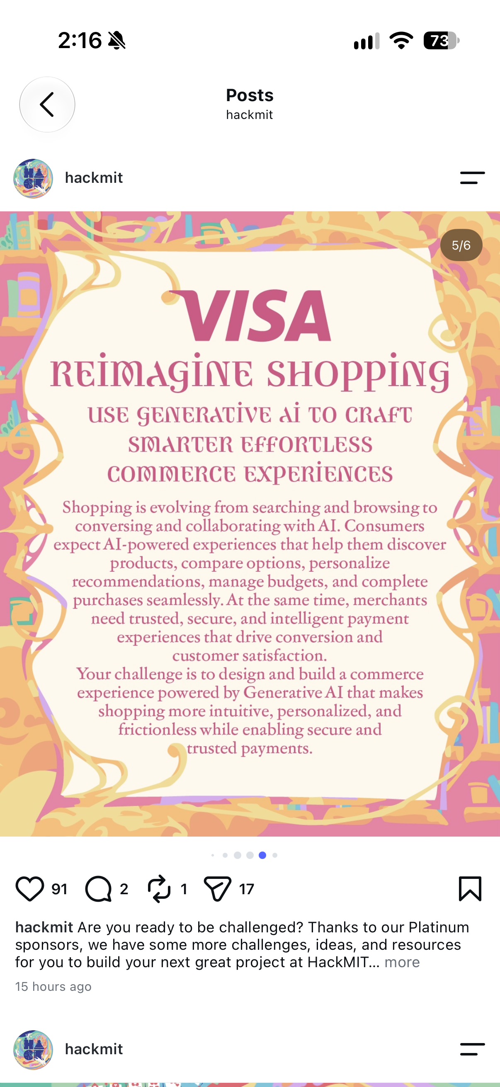
Sponsor Tracks/IMG_1975.jpeg
