adityuhkapoor/hack-mit-2026/Sponsor Tracks/IMG_1976.jpeg

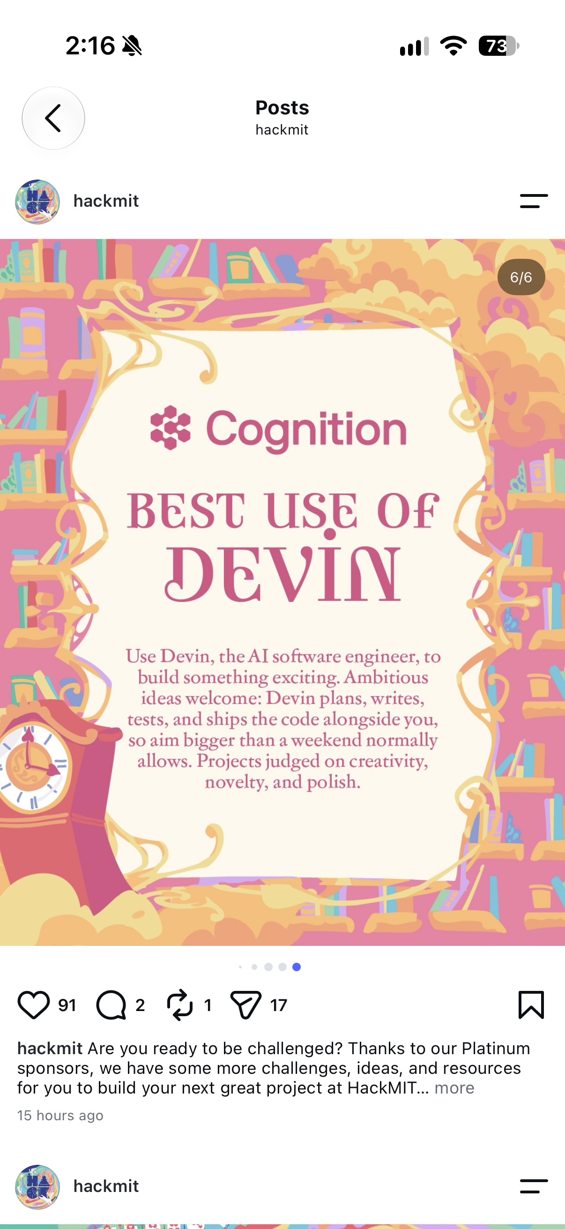
Sponsor Tracks/IMG_1976.jpeg
