adityuhkapoor/hack-mit-2026/Sponsor Tracks/IMG_1977.jpeg

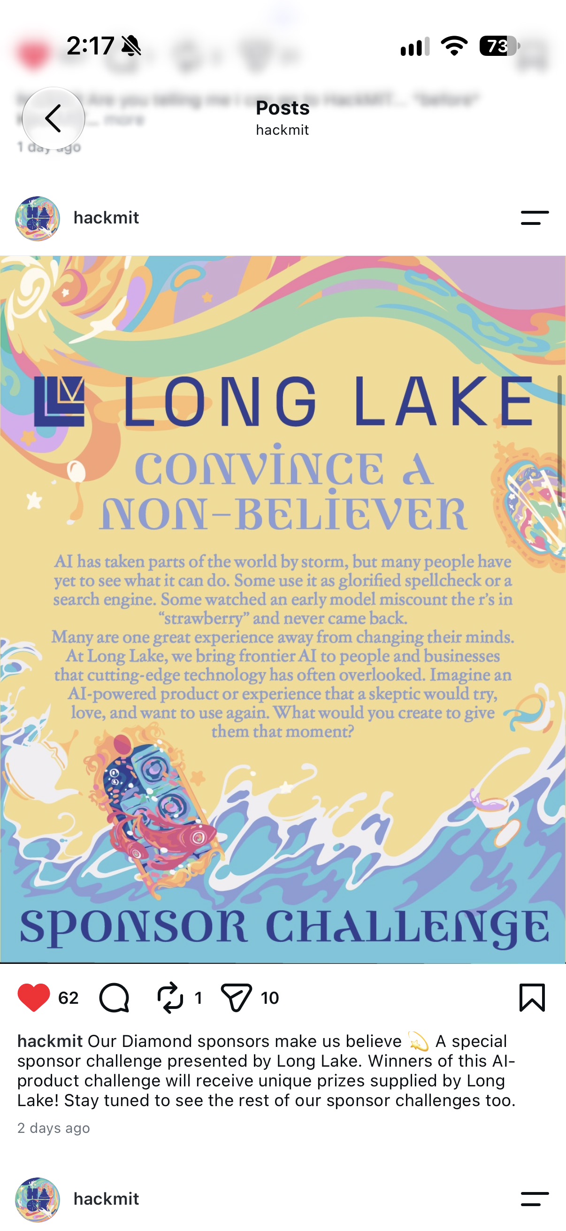
Sponsor Tracks/IMG_1977.jpeg
