adityuhkapoor/hack-mit-2026/Sponsor Tracks/IMG_1978.jpeg

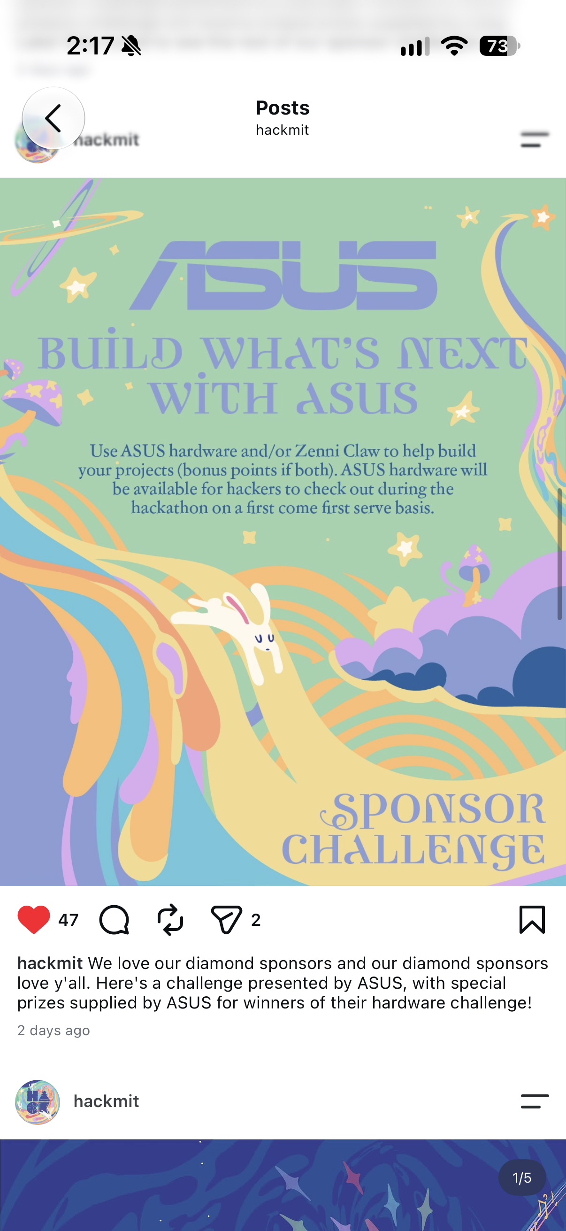
Sponsor Tracks/IMG_1978.jpeg
