adityuhkapoor/hack-mit-2026/design/modular-camera/assembled-rear.png

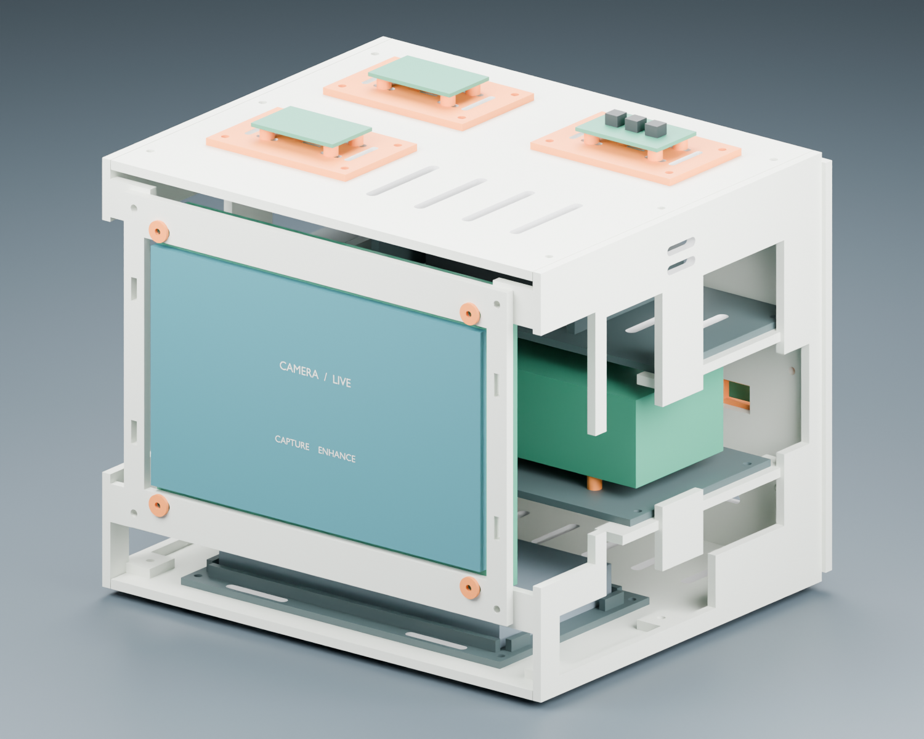
design/modular-camera/assembled-rear.png
